ramiss/FPVRaceOne/images/product_files/20260512_200925.jpg

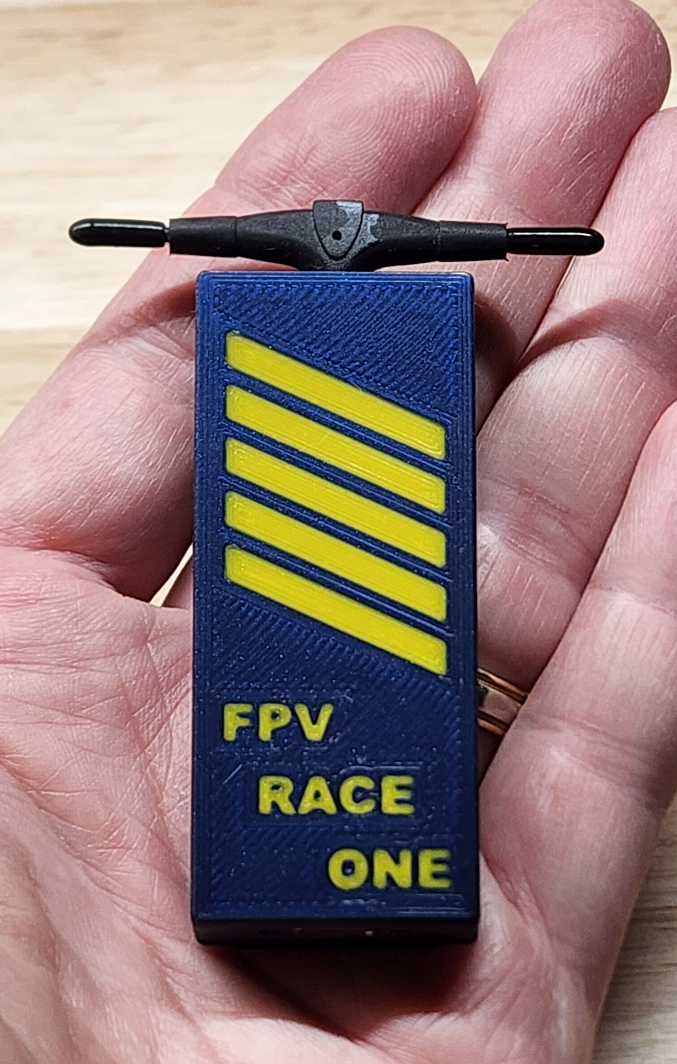
images/product_files/20260512_200925.jpg
