ramiss/FPVRaceOne/images/product_files/FPVRaceOne_Hero.png

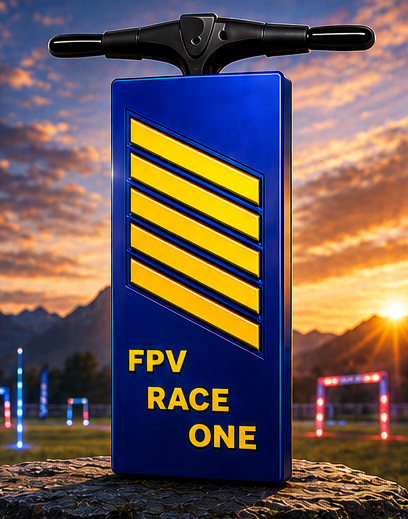
images/product_files/FPVRaceOne_Hero.png
