ramiss/FPVRaceOne/images/product_files/FPVRaceOne_Product.png

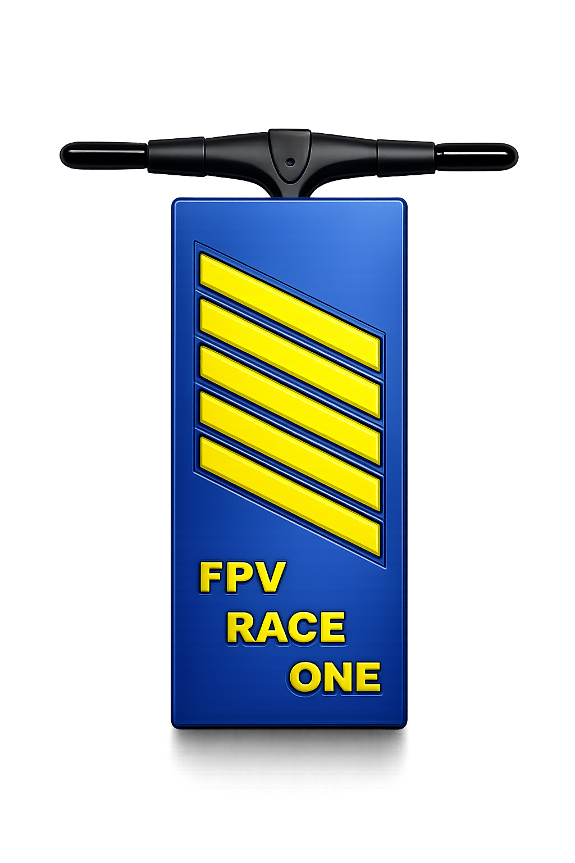
images/product_files/FPVRaceOne_Product.png
