ramiss/FPVRaceOne/images/screenshots/Screenshot 2.png

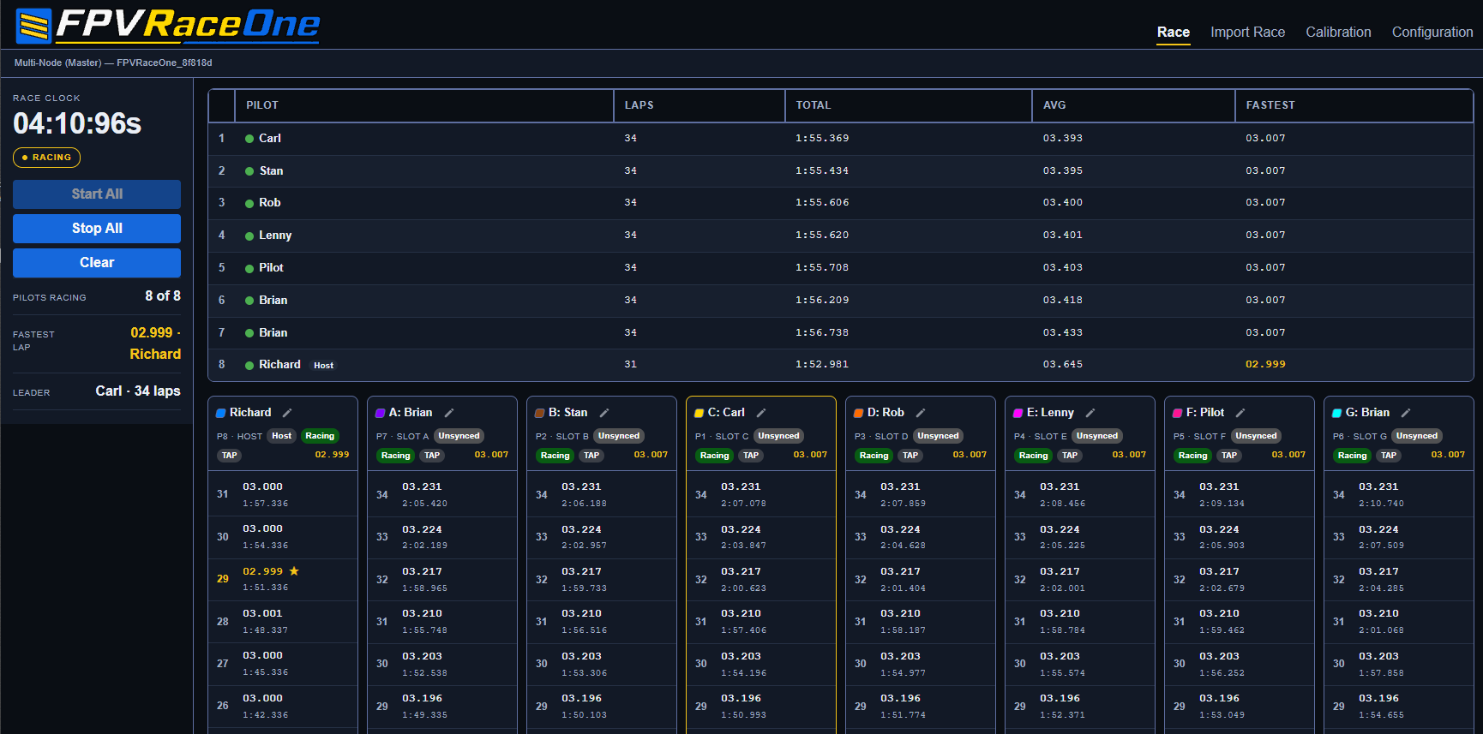
images/screenshots/Screenshot 2.png
