ramiss/FPVRaceOne/images/screenshots/Screenshot Settings 1.png

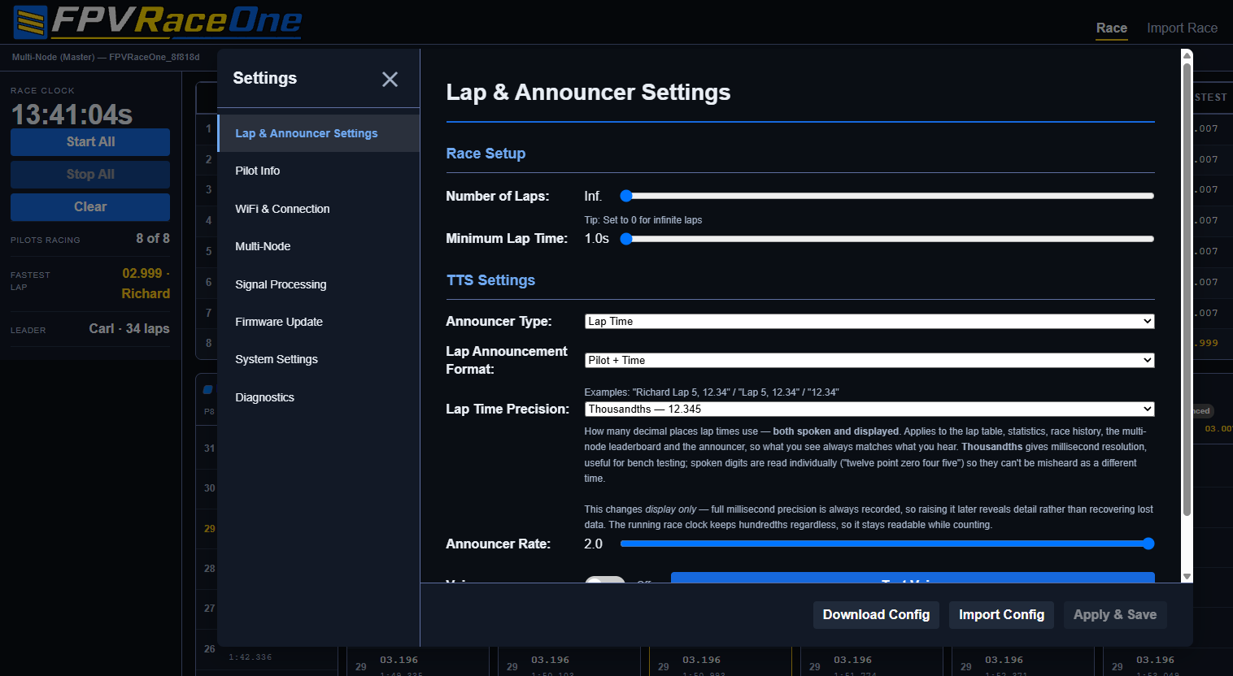
images/screenshots/Screenshot Settings 1.png
