ramiss/FPVRaceOne/images/screenshots/Screenshot Settings 4 Master.png

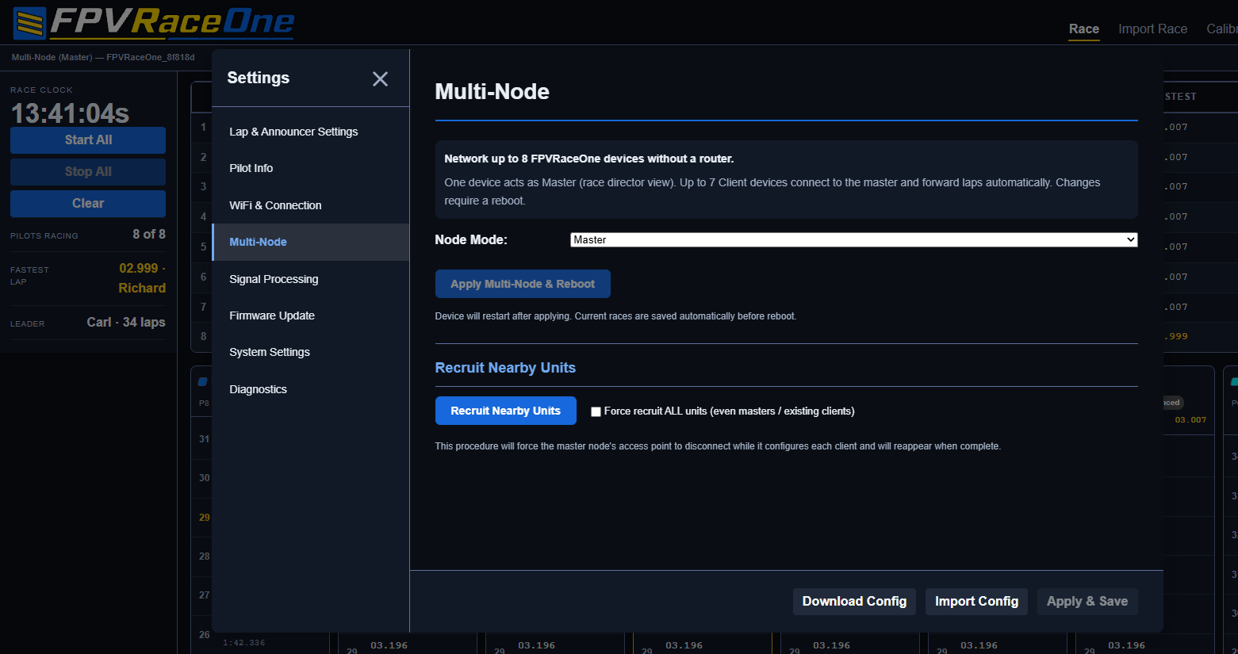
images/screenshots/Screenshot Settings 4 Master.png
