ramiss/FPVRaceOne/images/screenshots/Screenshot Settings 6.png

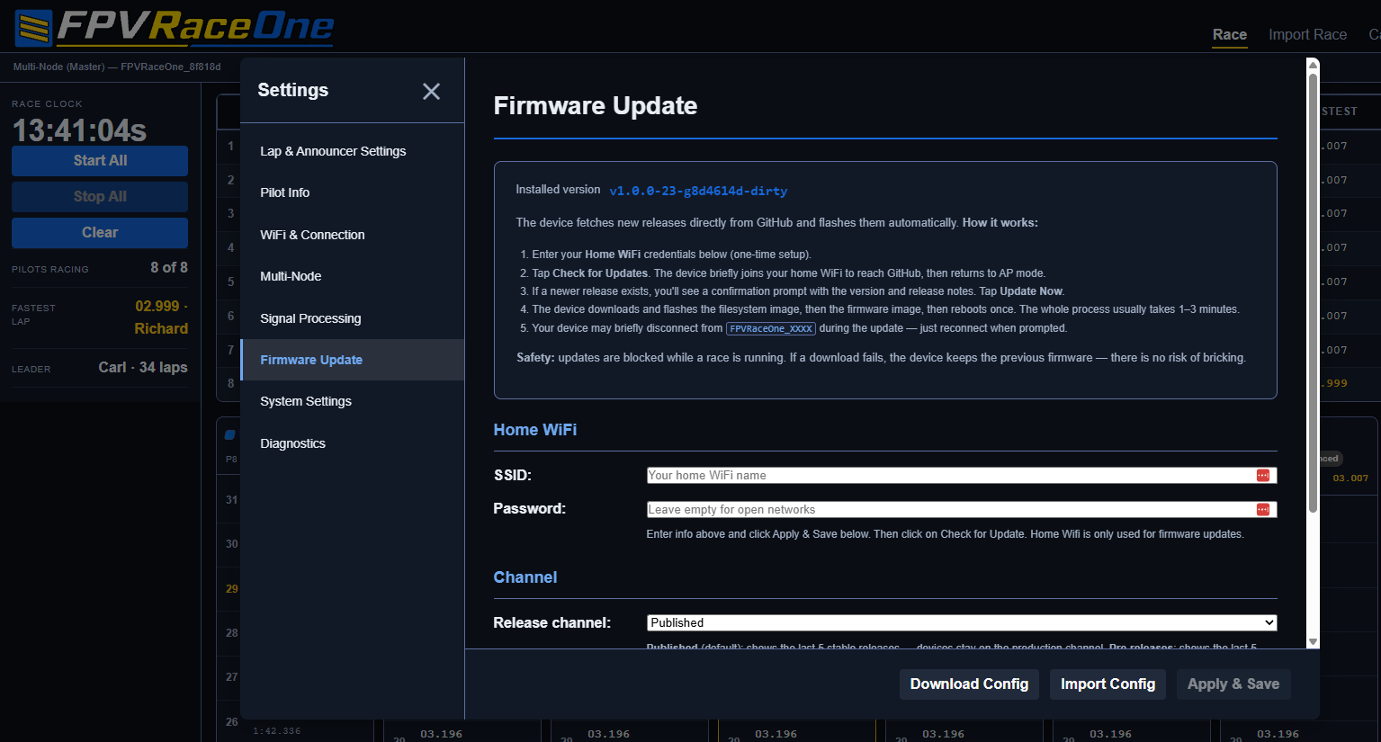
images/screenshots/Screenshot Settings 6.png
