ramiss/FPVRaceOne/images/screenshots/Screenshot Settings 7.png

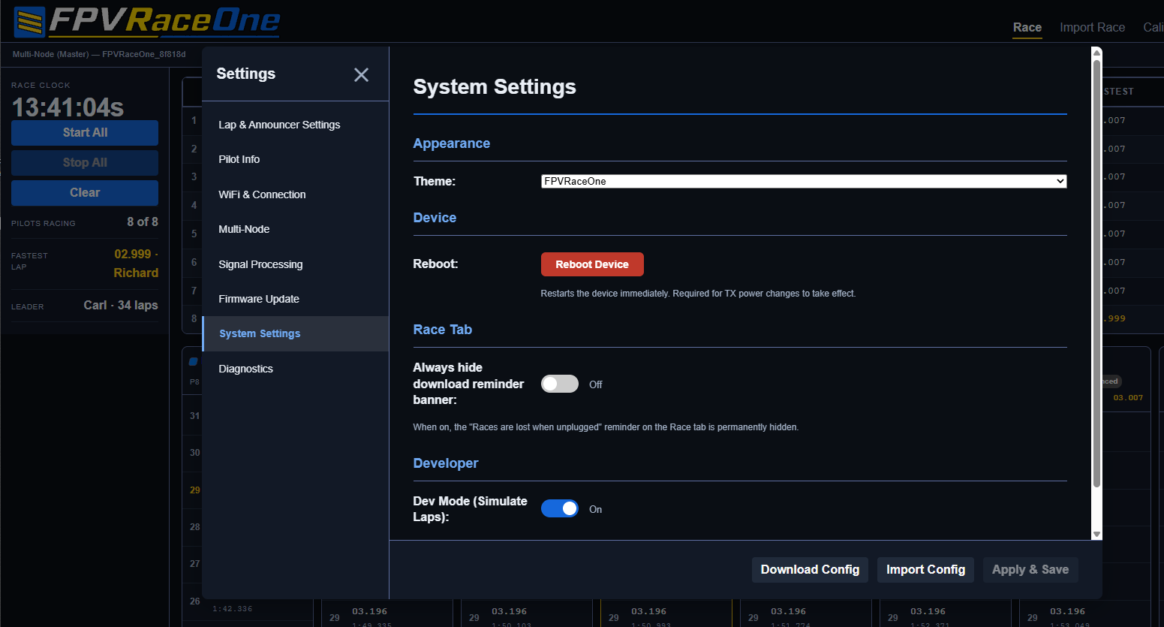
images/screenshots/Screenshot Settings 7.png
