ramiss/FPVRaceOne/images/screenshots/Screenshot Settings 8.png

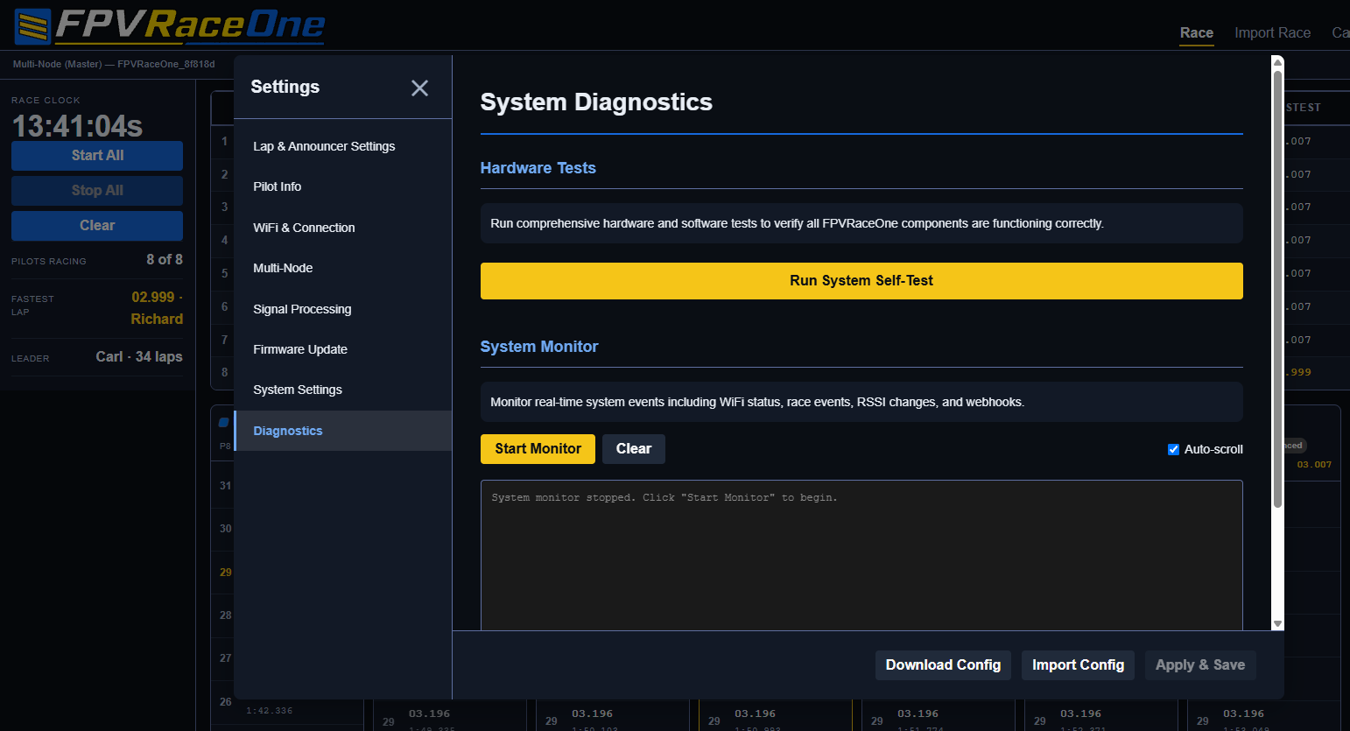
images/screenshots/Screenshot Settings 8.png
