ramiss/FPVRaceOne/images/screenshots/Screenshot Calibration.png

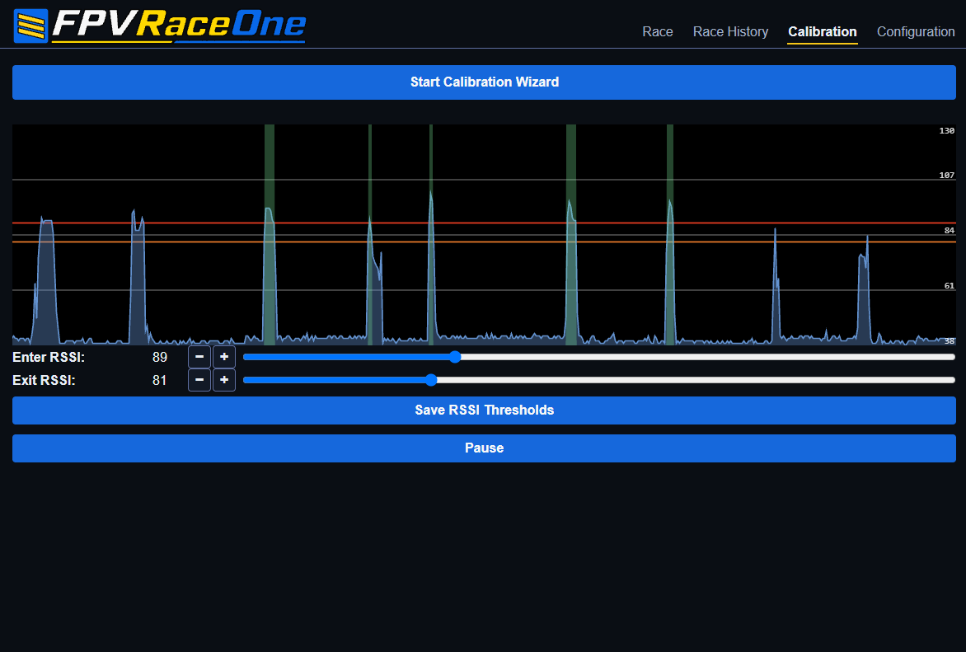
images/screenshots/Screenshot Calibration.png
