ramiss/FPVRaceOne/tools/timing-harness/gui.py

#!/usr/bin/env python3
"""
FPVRaceOne Timing Rig — GUI

Point-and-click front end for harness.py.  Runs the same measurements and adds
plain-language interpretation, because the raw numbers are easy to misread:
bias and jitter mean very different things, and only one of them actually costs
you a lap.

Tkinter deliberately: it ships with Python, so this runs on a clean Windows box
with nothing installed but pyserial (already needed for the harness itself).

    python gui.py

Measurement logic is imported from harness.py rather than duplicated, so the
CLI and GUI can never drift apart.
"""

import json
import os
import queue
import re
import statistics
import sys
import threading
import time
import tkinter as tk
from tkinter import ttk, scrolledtext

try:
    import serial
    from serial.tools import list_ports
except ImportError:
    sys.exit("pyserial not found. Install with:  pip install pyserial")

from harness import (JsonLink, run_once, summarize, open_port_no_reset,
                     measure_transfer, diagnose_transfer, EXPECTED_GAIN,
                     read_device_config, check_interval_vs_minlap, set_min_lap,
                     check_maxlaps_vs_count, emulator_handshake,
                     compute_thresholds, set_thresholds, _fit_line,
                     geometric_detect_ms, plan_envelope,
                     find_min_detectable_width, estimate_search_runs,
                     MultiNodeLoad, probe_master, set_voice_enabled,
                     fetch_director_state, time_director_post, client_targets,
                     fetch_clock_report, analyse_drift_series,
                     race_prearm, race_start, race_stop, fetch_race_clock,
                     DIRECTOR_FANOUT_MS, DIRECTOR_INTERVAL_MS)


# ── Dark theme ──────────────────────────────────────────────────────────────
#
# Picked to sit alongside the product's own dark UI rather than invent a second
# identity: slate panels, a teal accent, and status colours lifted toward the
# lighter end because saturated reds and greens that read well on white go muddy
# on a dark ground.
BG      = "#1a2226"   # window behind everything
PANEL   = "#222c31"   # frames and label frames
FIELD   = "#2a363c"   # entries, buttons, combobox wells
BORDER  = "#35454c"
FG      = "#e2e9ec"
MUTED   = "#93a5ad"
ACCENT  = "#17a589"   # FPVRaceOne teal
ACCENT_HI = "#1bbf9c"
OK_FG   = "#4ade80"
WARN_FG = "#fbbf24"
BAD_FG  = "#f87171"
HEAD_FG = "#ffffff"


def apply_dark_theme(root):
    """Recolour ttk + the classic Tk widgets that ttk styling never reaches."""
    st = ttk.Style()
    # 'clam' rather than 'vista': the native Windows themes draw most of their
    # elements from OS bitmaps and simply ignore background/foreground, so a
    # dark palette applied to them yields dark text on light chrome.
    try:
        st.theme_use("clam")
    except tk.TclError:
        pass

    root.configure(bg=BG)
    st.configure(".", background=PANEL, foreground=FG, fieldbackground=FIELD,
                 bordercolor=BORDER, lightcolor=PANEL, darkcolor=PANEL,
                 troughcolor=BG, focuscolor=ACCENT, insertcolor=FG)
    st.configure("TFrame", background=PANEL)
    st.configure("TLabel", background=PANEL, foreground=FG)
    st.configure("TLabelframe", background=PANEL, bordercolor=BORDER)
    st.configure("TLabelframe.Label", background=PANEL, foreground=ACCENT)
    st.configure("TButton", background=FIELD, foreground=FG,
                 bordercolor=BORDER, padding=(10, 5))
    st.map("TButton",
           background=[("disabled", PANEL), ("pressed", ACCENT),
                       ("active", ACCENT_HI)],
           foreground=[("disabled", MUTED), ("active", "#0f1416")])
    st.configure("TEntry", fieldbackground=FIELD, foreground=FG,
                 bordercolor=BORDER)
    st.configure("TSpinbox", fieldbackground=FIELD, foreground=FG,
                 arrowcolor=FG, bordercolor=BORDER)
    st.configure("TCombobox", fieldbackground=FIELD, background=FIELD,
                 foreground=FG, arrowcolor=FG, bordercolor=BORDER)
    st.map("TCombobox",
           fieldbackground=[("readonly", FIELD)],
           foreground=[("readonly", FG)],
           background=[("readonly", FIELD)])
    st.configure("TCheckbutton", background=PANEL, foreground=FG)
    st.map("TCheckbutton", background=[("active", PANEL)],
           indicatorcolor=[("selected", ACCENT)])
    st.configure("TScale", background=PANEL, troughcolor=FIELD)
    for bar in ("Vertical.TScrollbar", "Horizontal.TScrollbar"):
        st.configure(bar, background=FIELD, troughcolor=BG, arrowcolor=FG,
                     bordercolor=BORDER)
        st.map(bar, background=[("active", ACCENT)])
    # The status bar's sunken relief renders as a light bevel unless told
    # otherwise.
    st.configure("Status.TLabel", background=FIELD, foreground=MUTED,
                 padding=(6, 3))

    # A combobox's dropdown is a classic Tk listbox living in its own toplevel,
    # so no ttk style touches it — it stays glaring white without this.
    root.option_add("*TCombobox*Listbox.background", FIELD)
    root.option_add("*TCombobox*Listbox.foreground", FG)
    root.option_add("*TCombobox*Listbox.selectBackground", ACCENT)
    root.option_add("*TCombobox*Listbox.selectForeground", HEAD_FG)


def style_text_widget(w):
    """Dark-ground a classic Text/ScrolledText, including its caret+selection."""
    w.configure(background=BG, foreground=FG, insertbackground=FG,
                selectbackground=ACCENT, selectforeground=HEAD_FG,
                highlightthickness=0, borderwidth=0)


class FlowFrame(ttk.Frame):
    """A row of widgets that wraps to further rows as the window narrows.

    Tk has no flow layout: pack(side="left") runs children off the edge, and
    grid() shares column widths across rows, which makes ragged-width buttons
    align into gappy columns.  So children are positioned with place() and
    re-laid out on <Configure>, and the frame reports its own height.

    Needed because the button row alone is wider than the window's 760 px
    minimum — on a laptop the last tests were simply unreachable.
    """

    def __init__(self, master, hgap=6, vgap=6, **kw):
        super().__init__(master, **kw)
        self._items = []
        self._hgap = hgap
        self._vgap = vgap
        self._last_w = -1
        self.bind("<Configure>", self._on_configure)

    def add(self, widget, gap_before=0):
        """Append in flow order.  gap_before separates logical groups."""
        self._items.append((widget, gap_before))
        return widget

    def _on_configure(self, ev):
        # Reflow only on a real width change; <Configure> also fires for the
        # height changes we ourselves cause, which would recurse.
        if abs(ev.width - self._last_w) < 2:
            return
        self._last_w = ev.width
        self.reflow(ev.width)

    def reflow(self, width=None):
        if width is None:
            width = self.winfo_width()
        if width <= 1:
            return
        x = y = row_h = 0
        for w, gap_before in self._items:
            ww, wh = w.winfo_reqwidth(), w.winfo_reqheight()
            lead = gap_before if x else 0
            if x and x + lead + ww > width:
                x, y, row_h = 0, y + row_h + self._vgap, 0
                lead = 0
            w.place(x=x + lead, y=y, width=ww, height=wh)
            x += lead + ww + self._hgap
            row_h = max(row_h, wh)
        self.configure(height=y + row_h)


# ── Interpretation ──────────────────────────────────────────────────────────
#
# Thresholds are judgement calls, chosen so a "GOOD" verdict means the effect
# is well below anything that could matter in a race, not merely measurable.

# Mirrored from firmware so measured stalls can be expressed as a duty cycle.
# Keep in step with lib/MULTINODE/multinode.h and multinode.cpp.
FANOUT_THROTTLE_MS       = 2000.0   # MIN_DIRECTOR_BROADCAST_INTERVAL_MS
FANOUT_CLIENT_TIMEOUT_MS = 300      # http.setTimeout() in _broadcastDirectorState
FANOUT_RACE_TIMEOUT_MS   = 500      # http.setTimeout() in _broadcastRaceStart/Stop

JITTER_GOOD_MS = 5.0     # stdev below this is inaudible in a lap time
JITTER_WARN_MS = 15.0
BIAS_NOTE_MS   = 20.0    # bias worth mentioning for cross-device comparison
LAT_GOOD_MS    = 30.0


def _ms(us):
    """Microseconds -> a short millisecond string. '?' when the field is absent.

    Every start-path number on the wire is microseconds; every number a human
    reasons about here is milliseconds.  Converting at the point of display
    keeps the two from being confused in the same sentence.
    """
    if us is None:
        return "?"
    try:
        return "%.0f" % (float(us) / 1000.0)
    except (TypeError, ValueError):
        return "?"


def interpret_interval(res, st, interval_ms, geo_floor_ms=None):
    """Turn interval-test statistics into sentences that say what they mean.

    geo_floor_ms is the earliest a lap could possibly be confirmed for this
    pass width, from envelope geometry alone. Passing it lets the latency
    verdict judge pipeline lag rather than raw latency.
    """
    out = []

    # Before blaming detection, check the RIG actually produced the stimulus.
    # The emulator can reset or lose USB mid-run (a vanishing COM port is the
    # tell), and a stalled rig looks exactly like a device detecting nothing.
    if res.generated >= 0 and res.generated < res.expected:
        out.append(
            f"RIG FAULT — NOT A DEVICE PROBLEM: the emulator reports generating "
            f"only {res.generated} of {res.expected} passes. The device cannot "
            f"detect passes that were never played, so the miss count below is "
            f"the rig's, not the timer's. Check the emulator's USB connection "
            f"(a changing serial-port count is the tell) and re-run."
        )
    elif res.generated < 0:
        out.append(
            f"RIG WARNING: the emulator never sent its 'done' event, so the "
            f"number of passes actually played is unknown. Treat a high miss "
            f"count with suspicion until a clean run confirms the rig."
        )

    missed = res.expected - res.detected
    if missed > 0:
        out.append(
            f"MISSED PASSES: {missed} of {res.expected} generated passes produced "
            f"no lap. That is a detection failure, not a timing one — check the "
            f"enter/exit thresholds and the peak level before reading anything "
            f"below."
        )

    if not st:
        out.append("Not enough laps to compute statistics.")
        return out

    j = st["stdev_ms"]
    if j <= JITTER_GOOD_MS:
        out.append(
            f"CONSISTENCY: GOOD — {j:.2f} ms standard deviation. This is the "
            f"number that actually costs you a lap: lap-time error is the "
            f"difference in jitter between the two crossings, so low jitter "
            f"means repeatable lap times."
        )
    elif j <= JITTER_WARN_MS:
        out.append(
            f"CONSISTENCY: MARGINAL — {j:.2f} ms standard deviation. Visible in "
            f"a lap time but small against typical lap lengths. Worth checking "
            f"whether it grows under multi-node load."
        )
    else:
        out.append(
            f"CONSISTENCY: POOR — {j:.2f} ms standard deviation. Lap times will "
            f"vary noticeably run to run. Check Diagnostics -> RSSI Sample "
            f"Timing for a large worst-gap, which would point at a scheduling "
            f"stall."
        )

    b = st["bias_ms"]
    if abs(b) <= BIAS_NOTE_MS:
        out.append(
            f"BIAS: {b:+.2f} ms. Largely harmless on its own — the same delay "
            f"applies to both crossings of a lap and subtracts out. It matters "
            f"only when comparing two DIFFERENT devices head to head."
        )
    else:
        out.append(
            f"BIAS: {b:+.2f} ms — large. Still mostly cancels within a single "
            f"device's lap times, but two units with different bias would "
            f"disagree by roughly the difference in head-to-head racing."
        )

    if "lat_mean_us" in st:
        lm = st["lat_mean_us"] / 1000.0
        lj = st["lat_stdev_us"] / 1000.0

        # Judge the PIPELINE contribution, not raw latency.  A lap is confirmed
        # on gate exit, so most of the measured figure is simply "the pass had
        # to finish first" — a floor no firmware can beat.  An earlier version
        # compared raw latency against a flat 30 ms and called a perfectly
        # healthy 42 ms "HIGH", which was wrong and alarming.
        floor = geo_floor_ms
        if floor is not None:
            pipe = lm - floor
            if pipe <= 15.0:
                tag = "LATENCY GOOD"
            elif pipe <= 30.0:
                tag = "LATENCY MARGINAL"
            else:
                tag = "LATENCY HIGH"
            out.append(
                f"{tag}: {lm:.2f} ms total, of which {floor:.1f} ms is the pass "
                f"itself and only {pipe:.1f} ms is pipeline lag. A lap is "
                f"confirmed on gate EXIT, not at the peak, so a {res.width_ms} ms "
                f"pass cannot be detected sooner than {floor:.1f} ms no matter "
                f"what the firmware does. The {pipe:.1f} ms is median-filter "
                f"group delay plus the enter debounce."
            )
        else:
            out.append(
                f"LATENCY: {lm:.2f} ms mean, {lj:.2f} ms stdev, stimulus to "
                f"detection. Most of this is the pass width — a lap is confirmed "
                f"on gate exit, not at the peak."
            )

        # Separate real spread from outliers before drawing conclusions.
        if "lat_iqr_us" in st:
            iqr = st["lat_iqr_us"] / 1000.0
            med = st["lat_median_us"] / 1000.0
            outl = st.get("lat_outliers", 0)
            if lj > 2.0 * max(iqr, 0.01) and outl:
                out.append(
                    f"NOTE ON LATENCY SPREAD: stdev is {lj:.2f} ms but the "
                    f"inter-quartile range is only {iqr:.2f} ms, with {outl} "
                    f"outlier(s). The typical pass is tight — the stdev is being "
                    f"inflated by a few stray samples, not by genuine jitter. "
                    f"Median latency is {med:.2f} ms."
                )
            else:
                out.append(
                    f"LATENCY SPREAD: stdev {lj:.2f} ms, IQR {iqr:.2f} ms, "
                    f"median {med:.2f} ms. The two agree, so this is real "
                    f"spread rather than a few outliers."
                )

        if res.dropped:
            out.append(
                f"RIG NOTE: the emulator dropped {res.dropped} marker edge(s) "
                f"because a previous one had not been read yet. Those are lost "
                f"MEASUREMENTS, not missed detections — the device found the "
                f"laps. It only reduces the latency sample count."
            )

        out.append(
            f"IMPORTANTLY, THIS DOES NOT AFFECT LAP TIMES. Lap timing is "
            f"anchored to the recorded PEAK timestamp, not to when detection "
            f"finished, which is why bias is {st['bias_ms']:+.2f} ms despite "
            f"{lm:.0f} ms of detection latency. Latency jitter is {lj:.2f} ms "
            f"yet lap-time jitter is only {st['stdev_ms']:.2f} ms — the "
            f"peak-anchoring is measurably doing its job."
        )
    else:
        out.append(
            "ABSOLUTE LATENCY: not measured — no marker edges seen. Set "
            "TIMING_MARKER_ENABLED to 1 in lib/CONFIG/config.h, reflash, and "
            "confirm D3/GPIO21 is wired to the emulator's GPIO4."
        )

    return out


def interpret_sweep(rows):
    """rows: list of (width_ms, rate, stats-or-None)."""
    out = []
    reliable = [w for w, r, _ in rows if r >= 0.99]
    partial  = [w for w, r, _ in rows if 0.0 < r < 0.99]

    if reliable:
        best = min(reliable)
        out.append(
            f"MINIMUM RELIABLE PASS: {best} ms at >=99% detection. Shorter "
            f"passes than this start to be missed."
        )
        out.append(
            f"For context, a pass whose RSSI envelope is {best} ms wide is a "
            f"very fast gate transit. The narrower this number, the faster the "
            f"drone the pipeline can catch."
        )
    else:
        out.append(
            "NO WIDTH REACHED 99% DETECTION. Either the peak level is too close "
            "to the enter threshold, or calibration does not match the emulated "
            "envelope. Re-run the calibration wizard with the emulator "
            "connected, then retry."
        )

    if partial:
        out.append(
            f"PARTIAL DETECTION between {min(partial)} and {max(partial)} ms — "
            f"this is the roll-off band where the filter starts losing peaks."
        )

    out.append(
        "Compare this figure between polled and DMA modes. If they land in the "
        "same place, DMA peak-hold is not earning its complexity and polled is "
        "the simpler choice."
    )
    return out


# ── Window sizing ───────────────────────────────────────────────────────────

def fit_to_screen(win, want_w, want_h, min_w=760, min_h=520,
                  margin_w=40, margin_h=90):
    """Geometry string for want_w x want_h, shrunk to fit the actual display.

    The rig wants a tall results pane — reading test output is the whole point
    of the tool — but a window taller than the screen pushes the button row and
    the Stop button under the taskbar, where they cannot be clicked.  A short
    pane you can scroll beats a tall one you cannot reach, so the requested
    size is a CEILING, not a promise.

    margin_h covers a title bar plus a taskbar, margin_w a side dock.  Both are
    deliberately generous: losing 90 px of pane is invisible, losing the Stop
    button mid-soak is not.

    Positioned near the top-left rather than centred, so the raw-serial panel
    still has room to dock flush right on a wide display (see _dock_geometry).
    """
    win.update_idletasks()
    sw = win.winfo_screenwidth()
    sh = win.winfo_screenheight()
    w = max(min_w, min(want_w, sw - margin_w))
    h = max(min_h, min(want_h, sh - margin_h))
    x = max(0, min(20, sw - w))
    y = max(0, min(20, sh - h))
    return "%dx%d+%d+%d" % (w, h, x, y)


# ── GUI ─────────────────────────────────────────────────────────────────────

class TimingRigGUI:
    def __init__(self, root):
        self.root = root
        root.title("FPVRaceOne Timing Rig")
        # 1180 is the desktop target; fit_to_screen() clamps it on a laptop so
        # the button row never lands under the taskbar.
        root.geometry(fit_to_screen(root, 880, 1180))
        root.minsize(760, 520)

        self.q = queue.Queue()
        self.worker = None
        self.cancel = threading.Event()

        # Live-monitor state.  Buffers are bounded: this runs for hours between
        # tests and must not grow without limit.
        self._mon_thread = None
        # Ports a running test has claimed; the monitor must not reopen these.
        self._mon_claimed = set()
        self._mon_stop = threading.Event()
        self._mon_resume_after_test = False
        self._mon_lines = {"DUT": [], "EMU": []}
        self._MON_MAX_LINES = 20000
        # Raw serial goes to its own window rather than the results pane, so a
        # long-running monitor cannot bury the test output that gets shared.
        self._log_win = None
        self._log_text = {}
        self._log_follow = {}

        self._build_ports(root)
        self._build_settings(root)
        self._build_buttons(root)
        self._build_output(root)

        # Capture the as-built values BEFORE restoring, so "Reset to Defaults"
        # has something to go back to without re-reading the source.
        self._defaults = {k: v.get() for k, v in self._setting_vars().items()}
        self.restore_settings()

        self.refresh_ports()
        # Listen from launch.  The faults worth catching (the master rebooting
        # itself, the emulator panicking, clients cycling) happen while nobody
        # is running a test, so a monitor that only starts on demand misses
        # exactly the events it exists for.  Deferred slightly so the port
        # comboboxes and the drain loop are live first.
        if self.monitor_on.get():
            self.root.after(300, self._autostart_monitor)
        # Deferred: winfo_* returns 1x1+0+0 until the window manager has mapped
        # the window, so docking computed any earlier lands in the corner.
        if self.log_panel_auto.get():
            self.root.after(120, self._autodock_log_panel)
        self._update_sweep_estimate()   # traces only fire on edit, so seed it
        self.root.after(100, self._drain)

    # -- widgets ------------------------------------------------------------

    def _build_ports(self, root):
        f = ttk.LabelFrame(root, text="Serial ports", padding=8)
        f.pack(fill="x", padx=10, pady=(10, 4))

        ttk.Label(f, text="Emulator (WROOM-32):").grid(row=0, column=0, sticky="w")
        self.emu_cb = ttk.Combobox(f, width=46, state="readonly")
        self.emu_cb.grid(row=0, column=1, padx=6, pady=2)

        ttk.Label(f, text="FPVRaceOne (XIAO C6):").grid(row=1, column=0, sticky="w")
        self.dut_cb = ttk.Combobox(f, width=46, state="readonly")
        self.dut_cb.grid(row=1, column=1, padx=6, pady=2)

        ttk.Button(f, text="Refresh", command=self.refresh_ports)\
            .grid(row=0, column=2, padx=6)
        ttk.Button(f, text="Remember Ports", command=self.remember_ports)\
            .grid(row=1, column=2, padx=6)
        ttk.Button(f, text="Save Settings", command=self.save_settings)\
            .grid(row=0, column=3, padx=6)
        ttk.Button(f, text="Reset to Defaults", command=self.reset_settings)\
            .grid(row=1, column=3, padx=6)

        # Live monitor.  Several faults this session were only visible in raw
        # serial output that no test was capturing at the time — a floating
        # marker pin hanging the emulator, the master self-rebooting on low
        # heap, clients cycling between timeout and re-registration.  Watching
        # continuously, outside a test run, is how those get seen at all.
        self.monitor_on = tk.BooleanVar(value=True)
        # Panel opens docked on launch.  Untick to keep it closed; the choice
        # is saved with the other settings.
        self.log_panel_auto = tk.BooleanVar(value=True)
        ttk.Checkbutton(f, text="Live monitor", variable=self.monitor_on,
                        command=self._toggle_monitor)\
            .grid(row=0, column=4, padx=(12, 2), sticky="w")
        ttk.Button(f, text="Save Logs", command=self.save_logs)\
            .grid(row=1, column=4, padx=(12, 2), sticky="w")
        ttk.Button(f, text="Log Panel \u2197", command=self.open_log_panel)\
            .grid(row=0, column=5, padx=(6, 2))
        ttk.Checkbutton(f, text="auto-dock", variable=self.log_panel_auto)\
            .grid(row=1, column=5, padx=(6, 2), sticky="w")

    def _build_settings(self, root):
        # Settings are grouped by WHICH TEST USES THEM.  A single flat panel
        # put "Width" and "Sweep widths" side by side with no indication that
        # each is read by a different button and ignored by the other, which
        # is a fair way to confuse someone.
        self.vars = {}

        # ── Shared: the envelope every test drives the emulator with ────────
        f = ttk.LabelFrame(root, text="Signal — used by all tests", padding=8)
        f.pack(fill="x", padx=10, pady=(4, 2))

        def spin(parent, col, label, key, default, lo, hi, tip="", row=0):
            ttk.Label(parent, text=label).grid(row=row, column=col * 2,
                                               sticky="e", padx=(8, 2))
            v = tk.StringVar(value=str(default))
            ttk.Spinbox(parent, from_=lo, to=hi, textvariable=v, width=8)\
                .grid(row=row, column=col * 2 + 1, sticky="w")
            self.vars[key] = v
            if tip:
                ttk.Label(parent, text=tip, foreground="#666", font=("", 8))\
                    .grid(row=row + 1, column=col * 2, columnspan=2,
                          sticky="w", padx=(8, 2))

        spin(f, 0, "Baseline:", "baseline", 40, 0, 255, "at rest")
        spin(f, 1, "Peak:", "peak", 200, 0, 255, "at apex")
        spin(f, 2, "Interval (ms):", "interval", 3000, 100, 60000, "pass to pass")
        spin(f, 3, "Count:", "count", 30, 2, 500, "passes per run")

        # Min Lap discards any crossing sooner than its threshold (default
        # 5000 ms).  Zeroing it lets the rig use short intervals, which turns a
        # 16-minute sweep into about 4.  Restored afterwards.
        self.zero_minlap = tk.BooleanVar(value=False)
        ttk.Checkbutton(f, text="Force device Min Lap = 0 during run (restored after)",
                        variable=self.zero_minlap)\
            .grid(row=2, column=0, columnspan=8, sticky="w", padx=(8, 0), pady=(6, 0))

        # Announcements are rendered in the browser, never on the device, so
        # muting them cannot affect the measurement — it just spares a long
        # TTS backlog after a 30-lap run.
        self.mute_voice = tk.BooleanVar(value=False)
        ttk.Checkbutton(f, text="Mute device announcements during run "
                                "(restored after; refresh the browser tab to apply)",
                        variable=self.mute_voice)\
            .grid(row=3, column=0, columnspan=8, sticky="w", padx=(8, 0), pady=(2, 0))

        # ── Test 3 only ────────────────────────────────────────────────────
        f3 = ttk.LabelFrame(root, text="Test 3 only — Accuracy + Consistency",
                            padding=8)
        f3.pack(fill="x", padx=10, pady=2)
        spin(f3, 0, "Pass width (ms):", "width", 40, 1, 1000,
             "one fixed width; measures jitter at that width")

        # ── Test 4 only ────────────────────────────────────────────────────
        # Binary search rather than a hand-written list of widths: a list
        # spends most of its runs far from the boundary while still only
        # resolving to whatever spacing was typed.  The search halves until
        # detection fails, then bisects — same answer, fewer runs, and to a
        # stated precision.
        f4 = ttk.LabelFrame(root, text="Test 4 only — Min Pass Width "
                                       "(automatic search)", padding=8)
        f4.pack(fill="x", padx=10, pady=2)

        spin(f4, 0, "Start width (ms):", "sweep_start", 100, 5, 1000,
             "must detect reliably")
        spin(f4, 1, "Resolution (ms):", "sweep_res", 2, 1, 50,
             "how precisely to find it")
        spin(f4, 2, "Passes per step:", "sweep_count", 10, 3, 100,
             "more = slower, surer")
        spin(f4, 3, "Require (%):", "sweep_require", 90, 50, 100,
             "counts as 'detects'")

        # ── Multi-node load (optional, applies to tests 3 and 4) ───────────
        # Drives the master's expensive path — inbound lap -> blocking
        # directorState fanout to every registered client — at a known rate,
        # while the timing test runs underneath.  Real clients must be
        # registered: handleLap rejects unknown nodeIds and the fanout needs
        # somewhere to go.
        fL = ttk.LabelFrame(root, text="Multi-node load (optional) — applies to "
                                       "tests 3 and 4", padding=8)
        fL.pack(fill="x", padx=10, pady=2)

        self.load_on = tk.BooleanVar(value=False)
        ttk.Checkbutton(fL, text="Generate master load during the run",
                        variable=self.load_on)\
            .grid(row=0, column=0, columnspan=6, sticky="w", padx=(8, 0))

        # A master serves its AP on 192.168.5.1 (MULTINODE_MASTER_IP); a
        # single/standalone unit uses 192.168.4.1.  Default to the master
        # address, since load testing only applies in multi-node mode.
        ttk.Label(fL, text="Master IP:").grid(row=1, column=0, sticky="e", padx=(8, 2))
        self.master_ip = tk.StringVar(value="192.168.5.1")
        ttk.Entry(fL, textvariable=self.master_ip, width=16)\
            .grid(row=1, column=1, sticky="w")

        ttk.Label(fL, text="Node IDs:").grid(row=1, column=2, sticky="e", padx=(8, 2))
        self.load_nodes = tk.StringVar(value="1,2")
        ttk.Entry(fL, textvariable=self.load_nodes, width=12)\
            .grid(row=1, column=3, sticky="w")

        ttk.Label(fL, text="Pattern:").grid(row=1, column=4, sticky="e", padx=(8, 2))
        self.load_mode = tk.StringVar(value="burst")
        ttk.Combobox(fL, textvariable=self.load_mode, width=7, state="readonly",
                     values=("burst", "spread")).grid(row=1, column=5, sticky="w")

        ttk.Label(fL, text="Lap (s):").grid(row=1, column=6, sticky="e", padx=(8, 2))
        self.burst_interval = tk.StringVar(value="3.0")
        ttk.Entry(fL, textvariable=self.burst_interval, width=6)\
            .grid(row=1, column=7, sticky="w")

        ttk.Label(fL, text="Quiet before stop (s):").grid(row=2, column=4, sticky="e", padx=(8, 2))
        self.stop_delay = tk.StringVar(value="0")
        ttk.Entry(fL, textvariable=self.stop_delay, width=6)            .grid(row=2, column=5, sticky="w")
        ttk.Label(fL, text="Pack (ms):").grid(row=1, column=8, sticky="e", padx=(8, 2))
        self.burst_spread = tk.StringVar(value="10")
        ttk.Entry(fL, textvariable=self.burst_spread, width=6)\
            .grid(row=1, column=9, sticky="w")

        # Kept for 'spread' mode and for comparison against earlier results.
        self.load_rate = tk.StringVar(value="2.0")

        ttk.Label(fL, text="Source IPs:").grid(row=2, column=0, sticky="e", padx=(8, 2))
        self.load_srcs = tk.StringVar(value="")
        ttk.Entry(fL, textvariable=self.load_srcs, width=30)\
            .grid(row=2, column=1, columnspan=3, sticky="w", pady=(2, 0))
        ttk.Label(fL, text="blank = let the OS choose. Two comma-separated local "
                           "IPs splits the load across both WiFi adapters as "
                           "independent stations.",
                  foreground="#666", font=("", 8))\
            .grid(row=3, column=0, columnspan=6, sticky="w", padx=(8, 2))

        ttk.Button(fL, text="Check master", command=self.check_master)\
            .grid(row=1, column=6, padx=(10, 0))

        self.sweep_est = ttk.Label(f4, text="", foreground="#666", font=("", 8))
        self.sweep_est.grid(row=2, column=0, columnspan=8, sticky="w",
                            padx=(8, 2), pady=(6, 0))
        for k in ("sweep_start", "sweep_res", "sweep_count", "interval"):
            self.vars[k].trace_add("write", lambda *_: self._update_sweep_estimate())

        # Was needed when the polled and DMA paths had ~1.9x different ADC
        # gain: identical DAC values gave each mode a different RSSI envelope.
        # The firmware now scales the DMA path to match, so raw DAC values are
        # directly comparable again and this is OFF by default — leaving it on
        # would actually MASK a residual gain mismatch by silently correcting
        # for it, which is the opposite of what you want while verifying.
        #
        # Turn it on when the envelope must be pinned regardless of gain, e.g.
        # on a chip whose RSSI_DMA_GAIN_NUM has not been re-derived.
        self.target_rssi = tk.BooleanVar(value=False)
        ttk.Checkbutton(f, text="Baseline/Peak are RSSI targets (off = raw DAC; "
                                "on = pin the envelope regardless of gain)",
                        variable=self.target_rssi)\
            .grid(row=4, column=0, columnspan=8, sticky="w", padx=(8, 0), pady=(2, 0))

    def run_drift(self):
        # Needs NOTHING but the network.  Clock probing runs continuously in
        # steady state, so this neither starts a race nor touches a serial
        # port — both monitors stay live for the whole run.
        self._start(self._drift_worker, needs=())

    # ── Race sync ───────────────────────────────────────────────────────────
    #
    # Everything about the start path -- pre-arm, the clock-sync burst, the
    # scheduled fleet instant, the GO datagram, the ack, the repair pass -- was
    # built and debugged with no automated coverage, because the rig started
    # races over SERIAL and serial calls the timer directly.  Every regression
    # in that work was therefore caught by a human watching two screens.
    #
    # This drives the same three endpoints the director's browser drives, so
    # the real path runs, and then asserts the four things that path promises.
    RACE_SYNC_TOL_MS = 50.0        # cross-fleet start spread we accept
    RACE_SYNC_SETTLE_S = 12.0      # pre-arm window before GO; a countdown is ~18 s

    def run_race_sync(self):
        # Network only.  No serial, so both monitors stay live and the fleet
        # under test is the real one, not an emulator.
        self._start(self._race_sync_worker, needs=())

    def _race_sync_worker(self):
        try:
            master = self.master_ip.get().strip()
            try:
                rounds = max(1, int(self.sync_rounds.get()))
            except (TypeError, ValueError):
                rounds = 3

            self.emit("\n" + "=" * 66 + "\n", "dim")
            self.emit("RACE SYNC\n", "head")
            self.emit("Drives prearm -> GO -> stop over HTTP, %d time(s), and checks:\n"
                      "  1. every client acknowledged the GO datagram\n"
                      "  2. the fleet's race clocks agree within %.0f ms\n"
                      "  3. the start margin does NOT ratchet race over race\n"
                      "  4. a start with no pre-arm mints a FRESH race epoch\n"
                      "No quad required -- this measures the start path, not laps.\n\n"
                      % (rounds, self.RACE_SYNC_TOL_MS), "dim")

            nodes = probe_master(master)
            if not isinstance(nodes, dict):
                self.emit("  Master at %s did not answer. Needs master mode.\n"
                          % master, "bad")
                return
            targets = client_targets(nodes)
            if not targets:
                self.emit("  No online clients. This test needs at least one.\n", "bad")
                return
            self.emit("  %d client(s): %s\n\n"
                      % (len(targets),
                         ", ".join("%s(%s)" % (t[2], t[0]) for t in targets)), "dim")

            # Clean slate: a race left running from a previous session would
            # make round 1 measure a stop, not a start.
            race_stop(master)
            self.cancel.wait(1.5)

            boosts = []
            worst_spread = 0.0
            failures = []
            seen_race_ids = []

            for r in range(1, rounds + 1):
                if self.cancel.is_set():
                    break
                self.emit("  -- round %d --\n" % r, "head")
                st, _ = race_prearm(master)
                if st != 200:
                    failures.append("round %d: prearm returned %s" % (r, st))
                    self.emit("    prearm FAILED (%s)\n" % st, "bad")
                    break

                # Let the sync burst run.  Cutting this short does not just make
                # the test unrealistic -- it starves the very measurement the
                # start instant is computed from.
                self._await_sync(master, self.RACE_SYNC_SETTLE_S)

                st, _ = race_start(master)
                if st != 200:
                    failures.append("round %d: start returned %s" % (r, st))
                    self.emit("    start FAILED (%s)\n" % st, "bad")
                    break

                # Past the start margin (max 2.5 s) plus the verify grace, so
                # acks have landed and any repair has already happened.
                self.cancel.wait(4.0)

                spread, det = self._measure_start_spread(master, targets)
                rep = fetch_clock_report(master) or {}
                boost = rep.get("startBoostUs")
                if boost is not None:
                    boosts.append(boost)

                unacked = [n.get("nodeId") for n in rep.get("nodes", []) or []
                           if n.get("online") and n.get("clockValid")
                           and not n.get("startAcked")]
                late = [(n.get("nodeId"), n.get("startLateMs"))
                        for n in rep.get("nodes", []) or []
                        if (n.get("startLateMs") or 0) > 0]

                for line, tag in det:
                    self.emit(line, tag)
                if spread is not None:
                    worst_spread = max(worst_spread, spread)
                    self.emit("    start spread %.1f ms  (margin %s ms, boost %s ms)\n"
                              % (spread,
                                 _ms(rep.get("startMarginUs")), _ms(boost)),
                              "ok" if spread <= self.RACE_SYNC_TOL_MS else "bad")
                    if spread > self.RACE_SYNC_TOL_MS:
                        failures.append("round %d: start spread %.1f ms" % (r, spread))
                else:
                    failures.append("round %d: could not measure spread" % r)
                    self.emit("    could not read every node's clock\n", "bad")

                if unacked:
                    failures.append("round %d: no GO ack from node(s) %s"
                                    % (r, unacked))
                    self.emit("    NO GO ACK from node(s) %s -- these fell back to\n"
                              "    the HTTP repair path\n"
                              % ", ".join(str(x) for x in unacked), "bad")
                if late:
                    self.emit("    started late: %s\n"
                              % ", ".join("node %s +%s ms" % (a, b) for a, b in late),
                              "warn")

                ds = fetch_director_state(master)[1] or {}
                rid = (ds.get("race") or {}).get("raceId")
                seen_race_ids.append(rid)

                race_stop(master)
                self.cancel.wait(1.0)

                # After a stop the fleet must HOLD its final time, not zero it.
                ds = fetch_director_state(master)[1] or {}
                final = (ds.get("race") or {}).get("elapsedMs")
                if not final:
                    failures.append("round %d: master zeroed its clock on stop" % r)
                    self.emit("    master's clock reset to 0 on stop (should hold "
                              "the final time)\n", "bad")
                else:
                    self.emit("    final time held at %.2f s\n" % (final / 1000.0), "ok")
                self.cancel.wait(2.0)

            self._race_sync_epoch_check(master, seen_race_ids, failures)
            self._race_sync_verdict(boosts, worst_spread, failures)
        except Exception as e:
            self.emit("  Race sync failed: %s\n" % e, "bad")
        finally:
            try:
                race_stop(self.master_ip.get().strip())
            except Exception:
                pass

    def _await_sync(self, master, seconds):
        """Hold open the pre-arm window and report what the burst achieved."""
        deadline = time.time() + seconds
        best = {}
        while time.time() < deadline and not self.cancel.is_set():
            rep = fetch_clock_report(master)
            for n in (rep or {}).get("nodes", []) or []:
                if n.get("online") and n.get("clockValid"):
                    d = n.get("delayUs")
                    if d and d > 0:
                        nid = n.get("nodeId")
                        best[nid] = min(best.get(nid, d), d)
            self.cancel.wait(1.0)
        if best:
            self.emit("    synced %d node(s), best delay %.1f-%.1f ms\n"
                      % (len(best), min(best.values()) / 1000.0,
                         max(best.values()) / 1000.0), "dim")
        else:
            self.emit("    NO node reported a valid clock offset after %.0f s\n"
                      "    -- every start below will use the degraded HTTP path\n"
                      % seconds, "warn")

    def _measure_start_spread(self, master, targets):
        """Largest disagreement between any two race clocks, in ms.

        Each device is asked for its own elapsed, and each answer is corrected
        back to a common PC-clock instant.  A device that started early reads
        HIGH once corrected, so the spread across the fleet IS the start spread
        -- no device has to know about any other for this to work.
        """
        ref = time.time() + 0.001
        readings = []
        detail = []
        for ip, label in [(master, "master")] + [(t[1], "node %s" % t[0]) for t in targets]:
            ms, running, t_mid = fetch_race_clock(ip)
            if ms is None or not running:
                detail.append(("    %s: not running (%s)\n" % (label, ms), "bad"))
                continue
            corrected = ms - (t_mid - ref) * 1000.0
            readings.append((label, corrected))
        if len(readings) < 2:
            return None, detail
        lo = min(v for _, v in readings)
        for label, v in readings:
            detail.append(("    %-9s %8.0f ms  (%+6.1f ms)\n" % (label, v, v - lo), "dim"))
        return max(v for _, v in readings) - lo, detail

    def _race_sync_epoch_check(self, master, seen_race_ids, failures):
        """A start with NO pre-arm must mint a fresh epoch, not reuse the last.

        Reusing it is exactly the "run 2 inherits run 1's laps" failure the
        epoch system exists to prevent, and it is reachable in the field: a
        pre-arm POST that fails while the browser countdown proceeds anyway.
        """
        self.emit("\n  -- epoch check (start with no pre-arm) --\n", "head")
        # `or {}` on the inner get as well: a present-but-null "race" key would
        # make .get("race", {}) hand back None and crash mid-run, leaving a race
        # running on the fleet.  Same pattern as the round loop above.
        before = ((fetch_director_state(master)[1] or {}).get("race") or {}).get("raceId")
        st, _ = race_start(master)
        if st != 200:
            self.emit("    start returned %s -- skipped\n" % st, "warn")
            return
        self.cancel.wait(3.5)
        after = ((fetch_director_state(master)[1] or {}).get("race") or {}).get("raceId")
        race_stop(master)
        if before and after and before == after:
            failures.append("start without pre-arm reused epoch %s" % before)
            self.emit("    REUSED epoch %s -- a second race would inherit the\n"
                      "    first's laps\n" % before, "bad")
        else:
            self.emit("    epoch %s -> %s (fresh)\n" % (before, after), "ok")

    def _race_sync_verdict(self, boosts, worst_spread, failures):
        self.emit("\n  What this means\n", "head")
        if boosts:
            self.emit("    start boost across rounds: %s\n"
                      % " -> ".join(_ms(b) + " ms" for b in boosts), "dim")
            # The ratchet is the failure that hides: each race that "repairs" a
            # node adds 150 ms and only a perfectly clean race gives 25 ms back.
            # A pilot with "ignore race director" set made a clean race
            # impossible, so the margin climbed to its 1 s cap and stayed there.
            if len(boosts) >= 2 and boosts[-1] > boosts[0]:
                failures.append("start margin ratcheted: %s -> %s us"
                                % (boosts[0], boosts[-1]))
                self.emit("    RATCHETING: the boost grew across rounds, so some\n"
                          "    node is being counted as a missed start every race.\n"
                          "    Check for a client with 'ignore race director' set.\n",
                          "bad")
            else:
                self.emit("    boost is flat or decaying -- no phantom repairs.\n", "ok")

        if failures:
            self.emit("\n  FAILED (%d):\n" % len(failures), "bad")
            for f in failures:
                self.emit("    - %s\n" % f, "bad")
        else:
            self.emit("\n  PASS: every client acked GO, clocks agreed within\n"
                      "  %.1f ms (worst %.1f ms), the margin did not ratchet, and\n"
                      "  each race got its own epoch.\n"
                      % (self.RACE_SYNC_TOL_MS, worst_spread), "ok")

    def _drift_worker(self):
        """Log every node's raw clock offset, then fit drift over the whole run.

        WHY this exists: the firmware fits drift over a rolling 8-sample window
        (~1000 s span), which at the probe noise we measure gives a standard
        error near 6 ppm -- so its readings of -8/-5/+1/-4 ppm are all within
        1 sigma of zero and cannot be distinguished from no drift at all.
        A longer baseline shrinks that error as 1/span, so an hour of samples
        settles in minutes of analysis what the device cannot settle at all.

        Fits rawOffsetUs, never offsetUs: the latter is min-delay filtered and
        only steps when a better sample lands, so fitting it measures the
        filter rather than the crystals.

        The question is NOT "what is the drift" to high precision.  It is:
          1. is each node's value REPEATABLE (a per-unit crystal signature),
             or does it wander through the same range (noise)?
          2. does any node exceed ~10 ppm, the point where correcting it moves
             a lap by more than the offset error already does?
        """
        try:
            master = self.master_ip.get().strip()
            try:
                mins = max(1.0, float(self.drift_mins.get()))
            except (TypeError, ValueError):
                mins = 60.0
            period_s = 30.0

            self.emit("\n" + "=" * 66 + "\n", "dim")
            self.emit("CLOCK DRIFT LOG\n", "head")
            self.emit("Polls /api/multinode/clocks every %.0f s for %.0f min and fits\n"
                      "each node's raw offset over the whole run.\n"
                      "No race required -- drift probing runs continuously.\n\n"
                      % (period_s, mins), "dim")
            if mins < 30:
                self.emit("  NOTE: under 30 min the fit's error bar will still be\n"
                          "  several ppm, which is the size of the effect. 60+ min\n"
                          "  is what actually settles the question.\n\n", "warn")

            first = fetch_clock_report(master)
            if not isinstance(first, dict):
                self.emit("  Master at %s did not answer /api/multinode/clocks.\n"
                          "  Needs master mode and firmware with the clock report.\n"
                          % master, "bad")
                return

            # Same logs/ directory save_logs() uses, so a drift run lands
            # alongside the serial captures from the same session.
            out_dir = os.path.join(os.path.dirname(os.path.abspath(__file__)), "logs")
            os.makedirs(out_dir, exist_ok=True)
            stamp = time.strftime("%Y%m%d-%H%M%S")
            csv_path = os.path.join(out_dir, "%s-clockdrift.csv" % stamp)
            # (rawAtUs, rawOffsetUs, rawDelayUs, bootId) -- DEDUPED.  delay and
            # bootId travel WITH each sample rather than in a parallel list:
            # the analysis filters and segments on them, so they have to stay
            # aligned to the point they describe.
            series = {}      # nodeId -> [(at, off, delay, bootId)]
            ppm_hist = {}    # nodeId -> [firmware driftPpm readings]
            clamped = set()  # nodeIds whose firmware fit hit the +/-100 ppm rail
            reboots = {}     # nodeId -> count of bootId changes seen
            last_boot = {}   # nodeId -> last bootId seen
            last_at = {}     # nodeId -> rawAtUs of the sample already recorded
            dupes = 0

            deadline = time.time() + mins * 60.0
            polls = 0
            with open(csv_path, "w", encoding="utf-8", newline="") as fh:
                fh.write("wallClock,masterUs,rawAtUs,nodeId,rawOffsetUs,rawDelayUs,"
                         "offsetUs,delayUs,driftPpm,driftValid,driftClamped,"
                         "driftSamples,samples,bootId\n")
                while time.time() < deadline and not self.cancel.is_set():
                    rep = fetch_clock_report(master)
                    if isinstance(rep, dict):
                        polls += 1
                        m_us = rep.get("masterUs")
                        wall = time.strftime("%H:%M:%S")
                        for n in rep.get("nodes", []) or []:
                            if not isinstance(n, dict) or not n.get("online"):
                                continue
                            nid = n.get("nodeId")
                            raw = n.get("rawOffsetUs")
                            at  = n.get("rawAtUs")
                            if nid is None or raw is None:
                                continue
                            boot = n.get("bootId")
                            fh.write("%s,%s,%s,%s,%s,%s,%s,%s,%s,%s,%s,%s,%s,%s\n" % (
                                wall, m_us, at, nid, raw, n.get("rawDelayUs"),
                                n.get("offsetUs"), n.get("delayUs"),
                                n.get("driftPpm"), n.get("driftValid"),
                                n.get("driftClamped"),
                                n.get("driftSamples"), n.get("samples"), boot))
                            if n.get("driftValid"):
                                ppm_hist.setdefault(nid, []).append(n.get("driftPpm"))
                            # A clamped fit is the firmware saying "this reading
                            # ran away", not "this node drifts at 100 ppm".
                            if n.get("driftClamped"):
                                clamped.add(nid)
                            # Reboots are reported live: two clients restarting
                            # during an idle hour is its own defect, and burying
                            # it in the summary is how it went unnoticed before.
                            if boot and last_boot.get(nid) not in (None, boot):
                                reboots.setdefault(nid, []).append(
                                    n.get("resetReason") or "UNKNOWN")
                                self.emit("    node %s REBOOTED: %s  (bootId %s -> %s)\n"
                                          % (nid, n.get("resetReason") or "?",
                                             last_boot[nid], boot), "warn")
                            if boot:
                                last_boot[nid] = boot

                            # DEDUPE, and use the probe's OWN timestamp.
                            #
                            # Probing is round-robin at one node per 25 s, so on
                            # a six-client fleet each node yields a fresh sample
                            # only every ~150 s -- far slower than we poll.
                            # Counting the same sample five times would inflate
                            # n without adding information and shrink the error
                            # bar by ~sqrt(5), producing a confident number
                            # built on correlated points.  That is the exact
                            # mistake this tool exists to detect.
                            if at is None or last_at.get(nid) == at:
                                if at is not None:
                                    dupes += 1
                                continue
                            last_at[nid] = at
                            series.setdefault(nid, []).append(
                                (at, raw, n.get("rawDelayUs"), boot))
                        fh.flush()
                        if polls % 10 == 0:
                            left = max(0, deadline - time.time())
                            self.emit("    %d polls, %.0f min left\n" % (polls, left / 60.0),
                                      "dim")
                    # Interruptible sleep: Stop takes effect within the poll,
                    # not at the end of a 30 s nap.
                    self.cancel.wait(period_s)

            got = sum(len(v) for v in series.values())
            self.emit("\n  Wrote %s\n" % csv_path, "head")
            self.emit("  %d polls -> %d independent samples (%d repeat reads "
                      "discarded)\n" % (polls, got, dupes), "dim")
            self._report_drift(series, ppm_hist, clamped, reboots)
        except Exception as e:
            self.emit("  Drift log failed: %s\n" % e, "bad")

    def _report_drift(self, series, ppm_hist, clamped, reboots):
        """Independent fit + the repeatability test, side by side.

        Only nodes whose series is CLEAN reach `fits`.  A node that restarted
        mid-run is excluded outright rather than fitted: its esp_timer drops by
        its whole prior uptime, and a line through that step reports the uptime
        as a rate.  That is not a conservative reading, it is a wrong one, and
        it previously dominated the worst-case figure by five orders of
        magnitude.
        """
        self.emit("\n  What this means\n", "head")
        if not series:
            self.emit("  - No samples collected. Are clients online?\n", "bad")
            return

        MATERIAL_PPM = 10.0     # below this, correcting moves a lap < 3 ms / 5 min
        fits = {}
        excluded = []
        for nid in sorted(series):
            pts = series[nid]
            res = analyse_drift_series(pts)
            fw = ppm_hist.get(nid) or []
            fw_txt = ""
            if fw:
                fw_txt = "   firmware %+.0f..%+.0f ppm" % (min(fw), max(fw))
                if nid in clamped:
                    fw_txt += " (CLAMPED - not a measurement)"

            delays = [p[2] for p in pts if p[2]]
            med_delay = statistics.median(delays) if delays else 0

            if res["status"] == "discontinuity":
                excluded.append(nid)
                why = res["breaks"][0] if res["breaks"] else "series is not continuous"
                self.emit("    node %-2s  EXCLUDED - %s\n" % (nid, why), "bad")
                self.emit("              a fit across this would report the node's\n"
                          "              uptime as a drift rate, not its crystal.\n", "dim")
                continue
            if res["status"] == "implausible":
                excluded.append(nid)
                self.emit("    node %-2s  EXCLUDED - fit came out %+.0f ppm, beyond\n"
                          "              anything quartz does. Bad probes or an\n"
                          "              undetected restart.\n" % (nid, res["ppm"]), "bad")
                continue
            if res["status"] != "ok":
                self.emit("    node %-2s  not enough spread yet "
                          "(%d samples, %.0f min)\n"
                          % (nid, res["total_samples"], res["span_s"] / 60.0), "warn")
                continue

            ppm, se, n = res["ppm"], res["stderr"], res["n"]
            fits[nid] = (ppm, se)
            note = ""
            if res["segments"] > 1:
                note = "  [longest of %d segments]" % res["segments"]
            self.emit("    node %-2s  %+7.2f +/- %.2f ppm  (n=%d, delay med %.1f ms)%s%s\n"
                      % (nid, ppm, se, n, med_delay / 1000.0, fw_txt, note), "ok")

        if reboots:
            self.emit("\n  - %d node(s) RESTARTED during this run:\n" % len(reboots), "bad")
            for nid, why in sorted(reboots.items()):
                self.emit("      node %s x%d  %s\n"
                          % (nid, len(why), ", ".join(why)), "bad")
            # SW_RESTART on an idle fleet is the heap guard firing; PANIC and
            # TASK_WDT are crashes; BROWNOUT is the power rail, not the code.
            # Each points somewhere different, which is the whole reason the
            # reason is now carried on the heartbeat.
            self.emit("    Nothing was racing, so this is its own defect and worth\n"
                      "    chasing independently of drift. SW_RESTART = the heap\n"
                      "    guard; PANIC/TASK_WDT = a crash; BROWNOUT = power.\n", "dim")

        if not fits:
            self.emit("  - No clean series to fit. Need >= 8 samples spanning\n"
                      "    >= 5 min with no restart in the middle.\n", "warn")
            return
        if excluded:
            self.emit("  - Verdict below covers only the %d clean node(s); %s\n"
                      "    contributed nothing.\n"
                      % (len(fits), ", ".join("node %s" % x for x in excluded)), "dim")

        # ── Separate the COMMON MODE from the per-unit signal ────────────────
        #
        # Every ppm here is measured against the MASTER's crystal, so the
        # master's own rate is present, identically, in all of them.  A run
        # where all six nodes read -2.5..-6.1 ppm is not six drifting clients;
        # it is one fast master seen six times.  Reported raw, that common term
        # exceeds the error bars and gets announced as "RESOLVED: nodes 3, 6, 7
        # have real crystal drift" -- attributing the master's offset to three
        # arbitrary clients.
        #
        # It also points the MATERIALITY question at the wrong quantity.  A rate
        # every client shares shifts every lap identically and cancels out of
        # cross-pilot comparison; what can actually mis-order a race is the
        # SPREAD between clients.  So judge on residuals about the fleet median
        # (median, not mean: one genuinely bad crystal must not drag the
        # reference it is being judged against).
        common = None
        if len(fits) >= 3:
            common = statistics.median([p for p, _ in fits.values()])
            resid = {nid: p - common for nid, (p, _) in fits.items()}
            self.emit("\n  - COMMON MODE: every node reads %+.2f ppm against the\n"
                      "    master. That is the MASTER's crystal, not theirs --\n"
                      "    one fast master is a far likelier explanation than %d\n"
                      "    independent crystals all off by the same amount.\n"
                      "    Removing it leaves each node's own rate:\n"
                      % (common, len(fits)), "head")
            for nid in sorted(resid):
                se = fits[nid][1]
                sig = (abs(resid[nid]) / se) if (se == se and se > 0) else 0.0
                self.emit("        node %-2s  %+6.2f ppm  (%.2f sigma)\n"
                          % (nid, resid[nid], sig), "dim")
        else:
            resid = {nid: p for nid, (p, _) in fits.items()}
            self.emit("\n  - Only %d node(s): too few to separate the master's own\n"
                      "    rate from theirs, so the figures below still contain it.\n"
                      % len(fits), "warn")

        # Resolution and materiality are both judged on the RESIDUAL now.
        worst = max(abs(v) for v in resid.values())
        spread = max(resid.values()) - min(resid.values()) if len(resid) > 1 else 0.0
        resolved = [nid for nid, v in resid.items()
                    if fits[nid][1] == fits[nid][1] and fits[nid][1] > 0
                    and abs(v) > 2 * fits[nid][1]]

        self.emit("\n", "dim")
        if resolved:
            self.emit("  - RESOLVED: node(s) %s differ from the fleet by more than\n"
                      "    twice their own error bar, so that IS a per-unit crystal\n"
                      "    rate rather than noise.\n"
                      % ", ".join(str(x) for x in resolved), "ok")
        else:
            self.emit("  - NOT RESOLVED: once the master's common rate is removed,\n"
                      "    every node sits inside its own error bar. The fleet's\n"
                      "    crystals are indistinguishable from each other.\n", "warn")

        # Inter-pilot spread is the number that can actually mis-order a race.
        if worst >= MATERIAL_PPM:
            self.emit("  - MATERIAL: worst node is %.1f ppm from the fleet, moving\n"
                      "    its laps %.1f ms against its rivals across a 5-minute\n"
                      "    race -- above the offset error, so correcting is worth it.\n"
                      "    => gate driftValid on residual, then set CLOCK_APPLY_DRIFT.\n"
                      % (worst, worst * 0.3), "ok")
        else:
            self.emit("  - NOT MATERIAL: the whole fleet spans %.1f ppm = %.1f ms of\n"
                      "    inter-pilot skew across a 5-minute race, below the\n"
                      "    clock-offset error already in the system. Correcting it\n"
                      "    would add noise, not accuracy.\n"
                      "    => leave CLOCK_APPLY_DRIFT off; keep driftPpm as a\n"
                      "       hardware canary only.\n"
                      % (spread, spread * 0.3), "warn")
        if common is not None:
            self.emit("    (master vs clients carries the full %+.1f ppm = %.1f ms,\n"
                      "     and only within one race -- the anchor is re-taken at\n"
                      "     every start, so nothing accumulates across a session.)\n"
                      % (common, abs(common) * 0.3), "dim")

        self.emit("\n  This run was at ONE temperature. A null result here does not\n"
                  "  license disabling drift correction for good -- crystals are\n"
                  "  cut for ~25 C and a unit baking in the sun is the case that\n"
                  "  motivated the feature. Repeat with one node warmed and compare\n"
                  "  its ppm against its neighbours before deciding for the season.\n",
                  "dim")

    def run_fanout(self):
        # DUT only — the probe POSTs over WiFi and reads the master's serial;
        # the emulator is untouched, so its monitor stays live.
        self._start(self._fanout_worker, needs=("DUT",))

    def _fanout_worker(self):
        """Measure the directorState fanout the master cannot measure itself.

        The master only reports the AGGREGATE ("[CORE0] multinode blocked for
        N ms").  That number cannot distinguish "six clients each took 300 ms"
        from "five were instant and one ate the timeout", and those two call
        for completely different fixes.  So we fetch the real payload and time
        a POST of it to each client directly, from the PC, with a timeout long
        enough to measure the truth rather than truncate it at the 300 ms the
        firmware allows.

        Read-only: each client receives the same directorState it already gets
        twice a second, so this cannot disturb a race.
        """
        dut = None
        try:
            ports = self._links()
            if not ports:
                return
            _emu_p, dut_p = ports
            master = self.master_ip.get().strip()

            self.emit("\n" + "=" * 66 + "\n", "dim")
            self.emit("FANOUT PROBE\n", "head")
            self.emit("Times the directorState POST to each client individually.\n"
                      "The firmware allows each one %d ms (connect + read) and fans\n"
                      "out SEQUENTIALLY, so the whole cycle must finish inside\n"
                      "%d ms or parallelTask never gets idle time and SSE starves.\n\n"
                      % (DIRECTOR_FANOUT_MS, DIRECTOR_INTERVAL_MS), "dim")

            # 1. The real payload, exactly as the master fans it out.
            raw, parsed = fetch_director_state(master)
            if raw is None:
                self.emit("  Master at %s did not answer /api/multinode/nodes -- "
                          "is it powered and on this network?\n" % master, "bad")
                return
            self.emit("  Payload: %s bytes\n" % format(len(raw), ","), "head")

            if isinstance(parsed, dict):
                nodes = parsed.get("nodes", []) or []
                laps = 0
                arrays = False
                blockers = []      # online clients not advertising lapSync
                unknown = False    # firmware too old to publish the field
                for n in nodes:
                    if not isinstance(n, dict):
                        continue
                    try:
                        laps = max(laps, int(n.get("lapCount") or 0))
                    except (TypeError, ValueError):
                        pass
                    if isinstance(n.get("laps"), list):
                        arrays = True
                    nid = n.get("nodeId")
                    if not nid:
                        continue          # 0 == the master's own row
                    if "lapSync" not in n:
                        unknown = True
                    elif (n.get("online") and n.get("lapSyncHeard")
                          and not n.get("lapSync")):
                        # Only a node we have HEARD from that did not advertise
                        # lapSync is a blocker; not-yet-heard is not legacy.
                        age = n.get("lastSeenMs")
                        blockers.append((nid, n.get("pilotName") or "?", age))
                self.emit("  Highest lapCount seen: %d\n" % laps, "dim")

                if arrays:
                    self.emit("  Capability gate is SHUT -- nodes still carry full 'laps'\n"
                              "  arrays, so the payload grows with lap count and the heap\n"
                              "  win has not landed.\n", "bad")
                    if blockers:
                        # The gate is all-or-nothing, so ONE node closes it for
                        # the whole fleet. Naming it is the entire point.
                        self.emit("  Held shut by:\n", "bad")
                        for nid, name, age in blockers:
                            extra = ""
                            if isinstance(age, int):
                                extra = "  (last heartbeat %.1f s ago)" % (age / 1000.0)
                                if age > 10000:
                                    extra += "  <-- STALE, heartbeats not arriving"
                            self.emit("    node %-2s %s%s\n" % (nid, name, extra), "bad")
                        self.emit("  A node that is online but never advertises lapSync:1 is\n"
                                  "  either on older firmware or its heartbeats are being\n"
                                  "  rejected (a MAC mismatch 404s the heartbeat, and the\n"
                                  "  capability is only set on the heartbeat path).\n", "dim")
                    elif unknown:
                        self.emit("  Master firmware predates the per-node lapSync field, so\n"
                                  "  the blocker cannot be identified. Re-flash the MASTER to\n"
                                  "  get that diagnostic, then re-run.\n", "warn")
                    else:
                        self.emit("  ODD: every online client advertises lapSync, yet arrays\n"
                                  "  are still being emitted. Check for an node that is\n"
                                  "  registered-but-offline flapping online between the\n"
                                  "  payload build and this fetch.\n", "warn")
                else:
                    self.emit("  Digest-only payload (no per-node lap arrays) -- the\n"
                              "  capability gate is OPEN and payload size is bounded.\n",
                              "good")

            targets = client_targets(parsed)
            if not targets:
                self.emit("  No online clients in the payload -- nothing to probe.\n",
                          "warn")
                return

            # 2. Time each client on its own.
            rounds = 5
            self.emit("\n  Timing %d client(s), %d POSTs each (payload replayed "
                      "verbatim)\n\n" % (len(targets), rounds), "dim")
            results = []
            for nid, ip, _name in targets:
                if self.cancel.is_set():
                    return
                # Reachability first, with a SHORT timeout.  Five 4 s
                # timeouts per node meant an unreachable fleet took two
                # minutes to say so -- long enough to look like a hang.
                probe_ms, probe_status = time_director_post(ip, raw, timeout=1.5)
                if probe_status is None:
                    self.emit("    node %-2s %-15s UNREACHABLE (no response in 1.5 s)\n"
                              % (nid, ip), "bad")
                    results.append((nid, None))
                    continue
                times = [probe_ms]
                fails = 0
                for _ in range(rounds - 1):
                    if self.cancel.is_set():
                        return
                    ms, status = time_director_post(ip, raw, timeout=4.0)
                    if status is None:
                        fails += 1
                    else:
                        times.append(ms)
                    time.sleep(0.15)
                if times:
                    times.sort()
                    med = times[len(times) // 2]
                    over = med > DIRECTOR_FANOUT_MS
                    self.emit("    node %-2s %-15s min=%6.0f  med=%6.0f  max=%6.0f ms%s%s\n"
                              % (nid, ip, times[0], med, times[-1],
                                 "   TIMEOUT-BOUND" if over else "",
                                 ("  (%d failed)" % fails) if fails else ""),
                              "bad" if over else "good")
                    results.append((nid, med))
                else:
                    self.emit("    node %-2s %-15s answered once then stopped "
                              "(%d/%d failed)\n" % (nid, ip, fails, rounds), "bad")
                    results.append((nid, None))

            # 3. What the master itself reported over the same window.
            import re as _re
            dut = JsonLink(dut_p, name="dut", keep_log=True,
                           on_line=self._mon_sink("DUT"))
            self.emit("\n  Sampling the master's own fanout cost for 25 s...\n", "dim")
            blocked = []
            t0 = time.time()
            while time.time() - t0 < 25.0 and not self.cancel.is_set():
                for _ in dut.poll():
                    pass
                for line in dut.log[-40:]:
                    m = _re.search(r"multinode blocked for (\d+) ms", line)
                    if m:
                        v = int(m.group(1))
                        if not blocked or blocked[-1] != v:
                            blocked.append(v)
                time.sleep(0.2)

            # 4. Verdict.
            self.emit("\n  What this means\n", "head")
            timed = [r for r in results if r[1] is not None]
            slow = [r for r in timed if r[1] > DIRECTOR_FANOUT_MS]

            if timed:
                total = sum(r[1] for r in timed)
                self.emit("  - Sum of per-client medians: %.0f ms across %d client(s).\n"
                          % (total, len(timed)), "dim")

            if blocked:
                blocked.sort()
                med_blocked = blocked[len(blocked) // 2]
                self.emit("  - Master reported blocked %d-%d ms (median %d, %d samples).\n"
                          % (blocked[0], blocked[-1], med_blocked, len(blocked)), "dim")
                duty = 100.0 * med_blocked / DIRECTOR_INTERVAL_MS
                tag = "bad" if duty >= 80 else ("warn" if duty >= 50 else "good")
                self.emit("  - Fanout duty cycle: %.0f%% of the %d ms broadcast interval.\n"
                          % (duty, DIRECTOR_INTERVAL_MS), tag)
                if duty >= 80:
                    self.emit("    At this duty parallelTask is effectively always inside\n"
                              "    the fanout, which is what starves SSE and produces\n"
                              "    'not receiving updates' in the browser.\n", "bad")
            else:
                self.emit("  - No '[CORE0] multinode blocked' lines seen. Either the fanout\n"
                          "    is cheap right now, or DEBUG output is being dropped --\n"
                          "    check the Log Panel.\n", "warn")

            if slow:
                names = ", ".join(str(r[0]) for r in slow)
                self.emit("  - SLOW CLIENTS: node(s) %s exceed the %d ms the firmware\n"
                          "    allows, so the master eats its timeout on them every\n"
                          "    broadcast. Fixing those clients (or raising the timeout)\n"
                          "    is worth more than restructuring the fanout.\n"
                          % (names, DIRECTOR_FANOUT_MS), "bad")
            elif timed:
                self.emit("  - Every client answers inside %d ms individually. If the\n"
                          "    master still blocks ~2 s, the cost is the SEQUENTIAL fanout\n"
                          "    itself, not any one slow client -- the fix is to parallelise\n"
                          "    it or lengthen the interval.\n" % DIRECTOR_FANOUT_MS, "warn")
        except Exception as e:
            self.emit("  Fanout probe failed: %s\n" % e, "bad")
        finally:
            if dut:
                try:
                    dut.close()
                except Exception:
                    pass
            self.q.put(("done", None))

    def run_soak(self):
        # DUT only — the soak drives load over WiFi and never opens the
        # emulator, so the EMU monitor keeps logging throughout.
        self._start(self._soak_worker, needs=("DUT",))

    def _soak_worker(self):
        """Hold the device under load and watch heap over TIME, not passes.

        The other tests are bounded by pass count, so they end long before a
        slow allocation problem shows itself — a 90 s run finished with heap
        still above the floor and looked survivable, while a 180 s run at the
        same settings crossed it and the firmware rebooted itself.  What
        matters is the TREND: heap that plateaus is churn being reclaimed,
        heap that declines monotonically will eventually hit the floor no
        matter how healthy any single run looks.

        No emulator or detection involved.  This measures the master under
        multi-node traffic only.
        """
        dut = None
        load = None
        try:
            ports = self._links()
            if not ports:
                return
            emu_p, dut_p = ports
            try:
                mins = float(self.soak_mins.get())
            except ValueError:
                mins = 5.0
            secs = max(30.0, mins * 60.0)

            self.emit("\n" + "=" * 66 + "\n", "dim")
            self.emit("HEAP SOAK\n", "head")
            self.emit(f"Holds the master under multi-node load for {mins:g} "
                      f"minute(s) and tracks heap.\n"
                      f"The firmware reboots ITSELF below 20000 free or 8000 "
                      f"maxBlk sustained 10 s,\nso the question is whether "
                      f"either trends toward those floors.\n\n", "dim")

            dut = JsonLink(dut_p, name="dut", keep_log=True,
                           on_line=self._mon_sink("DUT"))

            load = self._make_load()
            if load:
                load.start()
                self.emit(f"  Load ACTIVE — {self._load_desc()}\n"
                          f"  to node(s) {self.load_nodes.get()} on "
                          f"{self.master_ip.get()}\n\n", "warn")
            else:
                self.emit("  No load configured — this measures IDLE heap "
                          "behaviour only.\n\n", "warn")

            import re as _re
            samples = []          # (t_s, free, maxBlk)
            t0 = time.time()
            last_report = 0.0
            rebooted = False
            while time.time() - t0 < secs and not self.cancel.is_set():
                for _ in dut.poll():
                    pass                       # JSON not needed; drives on_line
                for line in dut.log[-40:]:
                    m = _re.search(r"\[HEAP\] free=(\d+) min=(\d+) maxBlk=(\d+)", line)
                    if not m:
                        continue
                    rec = (int(m.group(1)), int(m.group(2)), int(m.group(3)))
                    if not samples or samples[-1][1:] != (rec[0], rec[2]):
                        samples.append((time.time() - t0, rec[0], rec[2]))
                if any("Initializing storage" in l for l in dut.log[-40:]):
                    rebooted = True
                    break
                el = time.time() - t0
                if el - last_report >= 30.0:
                    last_report = el
                    if samples:
                        _, f, b = samples[-1]
                        self.emit(f"    t+{el:4.0f}s   free={f:<7} maxBlk={b:<7}"
                                  f"  ({len(samples)} samples)\n", "dim")
                time.sleep(0.2)

            if load and load.started:
                load.stop()
                self.emit(f"\n  Load stopped: {load.sent} POST(s) accepted, "
                          f"{load.failed} failed\n", "dim")

            self.emit("\n  What this means\n", "head")
            if rebooted:
                self.emit("  - THE DEVICE REBOOTED during the soak. That is the "
                          "answer: it cannot sustain this load.\n", "bad")
                self._check_for_reboot(dut)
                return
            if len(samples) < 3:
                self.emit("  - Too few [HEAP] samples to judge. They are logged "
                          "every 5 s; run longer.\n", "warn")
                return

            # Judge the SECOND HALF only.  Heap settles sharply in the first
            # minute as caches fill and clients register, and an
            # endpoint-to-endpoint slope is dominated by that settling — it
            # reported "DECLINING, 1 minute to the floor" for a run whose maxBlk
            # had been dead flat at 14324 for the previous two minutes.  What
            # matters is whether it is STILL falling once steady state is
            # reached, not how far it fell getting there.
            half = samples[len(samples) // 2:]
            if len(half) < 3:
                half = samples
            t_span = (half[-1][0] - half[0][0]) or 1e-9
            d_free = half[-1][1] - half[0][1]
            d_blk  = half[-1][2] - half[0][2]
            min_free = min(x[1] for x in samples)
            min_blk  = min(x[2] for x in samples)
            free_rate = (d_free / t_span) * 60.0
            blk_rate  = (d_blk  / t_span) * 60.0

            self.emit(f"  - SETTLING (first half): free {samples[0][1]} -> "
                      f"{half[0][1]}, maxBlk {samples[0][2]} -> {half[0][2]}. "
                      f"Expected as caches fill.\n", "dim")
            self.emit(f"  - STEADY STATE (last {t_span:.0f}s): free {half[0][1]} "
                      f"-> {half[-1][1]} ({d_free:+}), maxBlk {half[0][2]} -> "
                      f"{half[-1][2]} ({d_blk:+}).\n"
                      f"    Lowest seen overall: free {min_free}, "
                      f"maxBlk {min_blk}.\n", "dim")
            self.emit(f"  - RATE (steady state): free {free_rate:+.0f} "
                      f"bytes/min, maxBlk {blk_rate:+.0f} bytes/min.\n", "dim")

            # maxBlk is what actually trips the watchdog, so project on it too.
            worst = None
            if free_rate < -200:
                worst = ("free", (half[-1][1] - 20000) / (-free_rate))
            if blk_rate < -200:
                t_blk = (half[-1][2] - 8000) / (-blk_rate)
                if worst is None or t_blk < worst[1]:
                    worst = ("maxBlk", t_blk)

            # A flat second half is the success condition and deserves saying
            # plainly, rather than being left to infer from a small slope.
            if abs(d_blk) < 1500 and abs(d_free) < 8000:
                worst = None
                self.emit(f"  - PLATEAU: maxBlk held at ~{half[-1][2]} and free "
                          f"at ~{half[-1][1]} across the last {t_span:.0f}s.\n"
                          f"    Allocation churn is being reclaimed — this is "
                          f"what a fixed heap looks like.\n", "good")

            if worst and worst[1] > 0:
                self.emit(f"  - DECLINING: at this rate {worst[0]} reaches its "
                          f"floor in about {worst[1]:.0f} more minute(s), and "
                          f"the firmware\n    will reboot itself. This is a "
                          f"real problem, not test noise.\n", "bad")
            elif worst:
                self.emit(f"  - ALREADY BELOW the {worst[0]} floor — a reboot is "
                          f"imminent.\n", "bad")
            else:
                self.emit(f"  - STABLE: neither figure is trending down "
                          f"meaningfully. Allocation churn is being reclaimed, "
                          f"so\n    heap is not the limiting factor at this "
                          f"load.\n", "good")
                if min_blk < 12000:
                    self.emit(f"    Note: maxBlk dipped to {min_blk}, within "
                              f"1.5x of the 8000 floor. Stable but not roomy.\n",
                              "warn")
        except Exception as e:
            self.emit(f"\nERROR: {e}\n", "bad")
        finally:
            try:
                if load and load.started:
                    load.stop()
            except Exception:
                pass
            if dut:
                dut.close()
            self.q.put(("done", None))

    def _build_buttons(self, root):
        # Wrapping row: seven test buttons plus the run controls are wider than
        # the window's own minimum, so on anything but a wide desktop the later
        # tests used to sit off-screen with no scrollbar to reach them.
        # Outer spacing via pack rather than ttk padding: place() coordinates
        # are relative to the widget's own origin and do not account for a ttk
        # frame's internal padding, so padding here would clip the bottom row
        # by however much was set.
        f = FlowFrame(root)
        f.pack(fill="x", padx=10, pady=4)
        self.btn_row = f

        self.btn_level = f.add(ttk.Button(f, text="1. Check Analog Path",
                                          command=self.run_level))
        self.btn_thresh = f.add(ttk.Button(f, text="2. Set Thresholds",
                                           command=self.run_thresholds))
        self.btn_interval = f.add(ttk.Button(f, text="3. Accuracy + Consistency",
                                             command=self.run_interval))
        self.btn_sweep = f.add(ttk.Button(f, text="4. Min Pass Width (Sweep)",
                                          command=self.run_sweep))
        self.btn_soak = f.add(ttk.Button(f, text="5. Heap Soak",
                                         command=self.run_soak))
        self.btn_fanout = f.add(ttk.Button(f, text="6. Fanout Probe",
                                           command=self.run_fanout))
        self.btn_drift = f.add(ttk.Button(f, text="7. Clock Drift Log",
                                          command=self.run_drift))
        self.btn_sync = f.add(ttk.Button(f, text="8. Race Sync",
                                         command=self.run_race_sync))

        f.add(ttk.Label(f, text="sync rounds:"), gap_before=10)
        self.sync_rounds = tk.StringVar(value="3")
        f.add(ttk.Entry(f, textvariable=self.sync_rounds, width=4))

        # gap_before marks a group boundary, so when the row wraps it prefers
        # to break between groups rather than mid-control.
        f.add(ttk.Label(f, text="soak mins:"), gap_before=10)
        self.soak_mins = tk.StringVar(value="5")
        f.add(ttk.Entry(f, textvariable=self.soak_mins, width=5))

        # Drift needs its OWN duration.  It used to share the soak's box, which
        # defaults to 5 -- and a 5-minute drift run yields ~2 samples per node,
        # below the 8-sample floor, so the tool simply refused to answer.  The
        # two runs want opposite defaults: a soak is short, a drift fit is long.
        f.add(ttk.Label(f, text="drift mins:"), gap_before=10)
        self.drift_mins = tk.StringVar(value="60")
        f.add(ttk.Entry(f, textvariable=self.drift_mins, width=5))

        self.btn_stop = f.add(ttk.Button(f, text="Stop", command=self.stop_run,
                                         state="disabled"), gap_before=10)
        f.add(ttk.Button(f, text="Clear", command=self.clear))

    def _build_output(self, root):
        f = ttk.LabelFrame(root, text="Results", padding=6)
        f.pack(fill="both", expand=True, padx=10, pady=(4, 10))

        # height is a FLOOR, not a target.  This is the only widget packed with
        # expand=True, so it absorbs whatever the window has left after the
        # fixed rows above it — which is how the pane grows to ~48 rows on the
        # desktop and shrinks gracefully on a laptop.  Requesting 48 here
        # instead would make the window's own requested size exceed a small
        # screen, and Tk would then clip the button row rather than the pane.
        self.out = scrolledtext.ScrolledText(f, wrap="word", height=12,
                                             font=("Consolas", 9))
        self.out.pack(fill="both", expand=True)
        style_text_widget(self.out)
        # Status colours are lifted toward the light end: the saturated red and
        # green that read well on white go muddy and low-contrast on a dark
        # ground, which is exactly where a "bad" line must not be easy to miss.
        self.out.tag_config("head", font=("Consolas", 10, "bold"),
                            foreground=HEAD_FG)
        self.out.tag_config("good", foreground=OK_FG)
        self.out.tag_config("ok",   foreground=OK_FG)
        self.out.tag_config("warn", foreground=WARN_FG)
        self.out.tag_config("bad",  foreground=BAD_FG)
        self.out.tag_config("dim",  foreground=MUTED)

        self.status = ttk.Label(root, text="Ready", style="Status.TLabel",
                                anchor="w")
        self.status.pack(fill="x", side="bottom")

    # -- helpers ------------------------------------------------------------

    # Where the chosen ports are remembered between sessions.  Keyed by USB
    # serial number, not COM port: COM numbers move when devices are re-plugged,
    # while the serial number is stable.
    _PREFS_PATH = os.path.join(os.path.dirname(os.path.abspath(__file__)),
                               "rig_settings.json")

    def _load_prefs(self):
        try:
            with open(self._PREFS_PATH, "r", encoding="utf-8") as fh:
                return json.load(fh)
        except Exception:
            return {}

    def _write_prefs(self, prefs):
        try:
            with open(self._PREFS_PATH, "w", encoding="utf-8") as fh:
                json.dump(prefs, fh, indent=2, sort_keys=True)
            return True
        except Exception as e:
            self.log(f"Could not save settings: {e}\n", "warn")
            return False

    def _load_port_prefs(self):
        return self._load_prefs().get("ports", {})

    def _save_port_prefs(self, ports):
        prefs = self._load_prefs()
        prefs["ports"] = ports
        self._write_prefs(prefs)

    def _setting_vars(self):
        """Every tk variable that represents a user setting.

        Discovered by type rather than listed by hand, so a setting added later
        is saved automatically instead of being silently forgotten — the usual
        way these files rot.
        """
        found = {}
        for name, val in vars(self).items():
            if name.startswith("_"):
                continue
            if isinstance(val, (tk.StringVar, tk.BooleanVar,
                                tk.IntVar, tk.DoubleVar)):
                found[name] = val
        for key, val in getattr(self, "vars", {}).items():
            found[f"vars.{key}"] = val        # the Signal spinboxes
        return found

    def save_settings(self):
        prefs = self._load_prefs()
        prefs["settings"] = {k: v.get() for k, v in self._setting_vars().items()}
        if self._write_prefs(prefs):
            self.log(f"Saved {len(prefs['settings'])} setting(s). They will be "
                     f"restored next time the GUI starts.\n", "good")

    def reset_settings(self):
        """Back to the values the GUI ships with, and forget the saved ones.

        Without this, one bad saved value (a 60000 ms interval, load pointed at
        a stale IP) persists across every future launch with no obvious way out
        short of deleting the file by hand.
        """
        for name, var in self._setting_vars().items():
            if name in getattr(self, "_defaults", {}):
                try:
                    var.set(self._defaults[name])
                except Exception:
                    pass
        prefs = self._load_prefs()
        prefs.pop("settings", None)          # ports are kept deliberately
        self._write_prefs(prefs)
        self.log("Settings reset to defaults and the saved copy cleared. "
                 "Remembered ports are kept.\n", "good")

    def restore_settings(self, quiet=False):
        saved = self._load_prefs().get("settings", {})
        if not saved:
            return
        applied = 0
        for name, var in self._setting_vars().items():
            if name not in saved:
                continue
            try:
                var.set(saved[name])
                applied += 1
            except Exception:
                pass      # a stale or renamed setting must not stop the rest
        if applied and not quiet:
            self.log(f"Restored {applied} saved setting(s).\n", "dim")

    @staticmethod
    def _serial_of(label):
        """Pull the USB serial number back out of a combobox label."""
        parts = label.split("  ")
        return parts[2].strip() if len(parts) >= 3 else ""

    def remember_ports(self):
        """Pin the current selections by USB serial number.

        Stored as serial numbers rather than COM ports because COM numbers are
        reassigned on re-plug, while the serial number (the device MAC on ESP32
        native USB) identifies one specific unit forever.
        """
        prefs = self._load_port_prefs()
        dut_sn = self._serial_of(self.dut_cb.get())
        emu_sn = self._serial_of(self.emu_cb.get())
        if dut_sn and dut_sn != "no-serial":
            prefs["dut"] = dut_sn
        if emu_sn and emu_sn != "no-serial":
            prefs["emu"] = emu_sn
        self._save_port_prefs(prefs)
        self.log(f"Remembered: FPVRaceOne={prefs.get('dut','-')}  "
                 f"emulator={prefs.get('emu','-')}\n"
                 f"  These are matched by serial number from now on, whatever "
                 f"COM port they land on.\n", "good")

    def refresh_ports(self):
        ports = list(list_ports.comports())
        prefs = self._load_port_prefs()
        labels, emu_guess, dut_guess = [], None, None
        pref_emu_label, pref_dut_label = None, None
        for p in ports:
            vid = f"{p.vid:04X}" if p.vid else "????"
            # On ESP32 native USB the serial number IS the device MAC, which is
            # the only reliable way to tell the master from its client units —
            # they all enumerate as 303A:1001 with identical descriptions.
            sn = p.serial_number or "no-serial"
            label = f"{p.device}  [{vid}]  {sn}  {p.description[:28]}"
            labels.append(label)
            if sn and sn == prefs.get("dut"):
                pref_dut_label = label
            if sn and sn == prefs.get("emu"):
                pref_emu_label = label
            # Same discriminator the upload task uses: Espressif native USB
            # (0x303A) is the XIAO C6; a bridge chip is the WROOM-32 devkit.
            if p.vid == 0x303A and dut_guess is None:
                dut_guess = label
            elif p.vid in (0x10C4, 0x1A86, 0x0403) and emu_guess is None:
                emu_guess = label

        self.emu_cb["values"] = labels
        self.dut_cb["values"] = labels

        # Auto-pick by USB VID, but never override a choice already made and
        # still present.  Every client unit is also a 0x303A ESP32-C6, so
        # "first native-USB port found" is not reliably the master — once the
        # operator has picked the right one, a refresh must not silently move
        # the test to a different device.
        # Priority: remembered serial number > current selection > VID guess.
        def _pick(cb, remembered, guess):
            if remembered:
                cb.set(remembered)
                return remembered, True
            cur = cb.get()
            if cur and cur in labels:
                return cur, False        # still connected — leave it alone
            if guess:
                cb.set(guess)
                return guess, False
            return None, False

        _pick(self.emu_cb, pref_emu_label, emu_guess)
        dut_sel, dut_remembered = _pick(self.dut_cb, pref_dut_label, dut_guess)

        self.log(f"Found {len(ports)} serial port(s).\n", "dim")
        if dut_remembered:
            self.log(f"  FPVRaceOne restored from saved serial "
                     f"{self._serial_of(dut_sel)} on {dut_sel.split()[0]}.\n", "good")
        else:
            n303a = sum(1 for p in ports if p.vid == 0x303A)
            if n303a > 1 and dut_sel:
                self.log(f"  {n303a} devices share VID 0x303A (client units are "
                         f"ESP32-C6 too). Pick the master, then press Remember "
                         f"Ports\n  so it is matched by serial number "
                         f"(= its MAC) from now on.\n", "warn")

    @staticmethod
    def _port_of(label):
        return label.split()[0] if label else None

    # ── Live serial monitor ────────────────────────────────────────────
    def _autostart_monitor(self):
        """Deferred launch start — re-check the toggle at FIRE time.

        Checking only at schedule time was a race: switching the monitor off
        within the first 300 ms still let it grab the ports afterwards, so the
        checkbox and reality disagreed.
        """
        if self.monitor_on.get():
            self._start_monitor()

    def _toggle_monitor(self):
        if self.monitor_on.get():
            self._start_monitor()
        else:
            self._stop_monitor()

    def _start_monitor(self, watch=("DUT", "EMU"), quiet=False):
        """Start the raw-serial monitor over `watch` ports only.

        `watch` exists so a test that claims one port does not silence the
        other.  The soak and the fanout probe only ever open the DUT, so the
        emulator has no reason to go dark for five minutes — and a gap in the
        EMU log during a run is exactly when you want to know whether the
        emulator was still alive.
        """
        if self._mon_thread and self._mon_thread.is_alive():
            return
        if not watch:
            return
        if self.worker and self.worker.is_alive() and set(watch) & self._mon_claimed:
            self.log("Cannot monitor a port a running test has claimed.\n", "warn")
            return
        ports = self._links()
        if not ports:
            self.monitor_on.set(False)
            return
        emu_p, dut_p = ports
        self._mon_stop.clear()
        self._mon_thread = threading.Thread(
            target=self._monitor_worker, args=(emu_p, dut_p, tuple(watch)),
            daemon=True)
        self._mon_thread.start()
        if quiet:
            # _stop_monitor() unticked the box on its way out.  Re-tick it:
            # the monitor IS running, just on fewer ports, and a checkbox
            # reading "off" while the EMU pane fills up is worse than useless.
            # Same programmatic .set() the done-handler already relies on, so
            # it does not re-enter the widget command.
            self.monitor_on.set(True)
            names = ", ".join(sorted(watch))
            self.log(f"  Live monitor continues on {names} "
                     f"(the other port is held by the test).\n", "dim")
            return
        self.log(f"Live monitor ON — FPVRaceOne {dut_p}, emulator {emu_p}. "
                 f"Raw output, nothing filtered.\n"
                 f"  Open 'Log Panel' to view it. The ports are held while "
                 f"monitoring, so untick Live monitor before flashing from "
                 f"PlatformIO.\n", "good")

    def _stop_monitor(self):
        self._mon_stop.set()
        t = self._mon_thread
        if t:
            t.join(timeout=2.0)
        self._mon_thread = None
        self.monitor_on.set(False)

    def _monitor_worker(self, emu_p, dut_p, watch=("DUT", "EMU")):
        """Read the watched ports raw and stream them to the log panel.

        Deliberately does NOT parse or filter.  Every diagnostic gap this
        session came from a filter dropping the one line that mattered — the
        panic, the [HEAP] FATAL, the [CORE0] stall.  Raw means raw.

        Each port reconnects independently.  Both boards reset in normal use —
        the master on its own low-heap watchdog, the emulator when its port is
        opened — and a monitor that gave up on the first read error would go
        silent precisely when something interesting had just happened.
        """
        all_targets = {"DUT": dut_p, "EMU": emu_p}
        targets = {k: v for k, v in all_targets.items() if k in watch}
        handles = {}          # name -> serial handle (absent = needs opening)
        buffers = {k: "" for k in targets}
        next_try = {k: 0.0 for k in targets}
        announced = set()

        def _open(name):
            now = time.time()
            if now < next_try[name]:
                return
            next_try[name] = now + 2.0        # retry cadence while unplugged
            try:
                handles[name] = open_port_no_reset(targets[name])
                if name in announced:
                    self.emit_mon_status(name, f"  Monitor: {name} reconnected "
                                               f"on {targets[name]}.\n", "good")
                    announced.discard(name)
            except Exception as e:
                if name not in announced:
                    hint = ""
                    if "denied" in str(e).lower() or "access" in str(e).lower():
                        hint = ("\n     Another program holds that port — a "
                                "PlatformIO/VSCode serial monitor, PuTTY, or a "
                                "second copy\n     of this GUI. Close it and "
                                "the monitor will reconnect on its own.")
                    self.emit_mon_status(name,
                        f"  Monitor: cannot open {name} on {targets[name]} — "
                        f"{e}{hint}\n", "bad")
                    announced.add(name)

        try:
            while not self._mon_stop.is_set():
                for name in targets:
                    if name not in handles:
                        _open(name)
                        continue
                    try:
                        data = handles[name].read(4096).decode("utf-8",
                                                               errors="replace")
                    except Exception as e:
                        # Port vanished (board reset / cable). Drop it and let
                        # the reconnect loop pick it up again.
                        try:
                            handles[name].close()
                        except Exception:
                            pass
                        handles.pop(name, None)
                        self.emit_mon_status(name, f"  Monitor: {name} "
                                                   f"disconnected — {e}\n", "bad")
                        announced.add(name)
                        continue
                    if not data:
                        continue
                    buffers[name] += data
                    while "\n" in buffers[name]:
                        line, buffers[name] = buffers[name].split("\n", 1)
                        line = line.rstrip("\r")
                        if not line:
                            continue
                        stamp = time.strftime("%H:%M:%S")
                        rec = f"{stamp} [{name}] {line}"
                        lines = self._mon_lines[name]
                        lines.append(rec)
                        if len(lines) > self._MON_MAX_LINES:
                            del lines[:len(lines) - self._MON_MAX_LINES]
                        tag = self._mon_tag(line)
                        # The emulator heartbeat carries tickHz — the timer ISR
                        # rate.  It should sit at TICK_HZ whether or not a run
                        # is playing, so zero means the DAC has stopped being
                        # driven.  Call that out rather than leave an operator
                        # to notice one number among thousands of lines.
                        if name == "EMU" and '"event":"hb"' in line.replace(" ", ""):
                            m = re.search(r'"tickHz"\s*:\s*(\d+)', line)
                            if m:
                                hz = int(m.group(1))
                                if hz == 0:
                                    tag = "bad"
                                    self.emit_mon(name,
                                        "--- EMULATOR DAC STOPPED: tickHz=0, the "
                                        "envelope timer ISR is not running ---\n",
                                        "bad")
                                elif hz < 9000 or hz > 11000:
                                    tag = "warn"
                        if name == "EMU" and '"rst"' in line and "POWERON" not in line \
                                and "EXT_RESET" not in line:
                            self.emit_mon(name,
                                "--- EMULATOR RESTARTED for a non-normal reason "
                                "(see rst= above) ---\n", "bad")
                        self.emit_mon(name, rec + "\n", tag)
                time.sleep(0.02)
        finally:
            for sp in handles.values():
                try:
                    sp.close()
                except Exception:
                    pass
            self.emit("  Live monitor OFF.\n", "dim")

    def save_logs(self):
        """Write the monitor buffers and the on-screen results to text files."""
        out_dir = os.path.join(os.path.dirname(os.path.abspath(__file__)), "logs")
        try:
            os.makedirs(out_dir, exist_ok=True)
        except Exception as e:
            self.log(f"Could not create {out_dir}: {e}\n", "bad")
            return
        stamp = time.strftime("%Y%m%d-%H%M%S")
        written = []
        for name in ("DUT", "EMU"):
            lines = self._mon_lines.get(name, [])
            if not lines:
                continue
            path = os.path.join(out_dir, f"{stamp}-{name.lower()}-serial.txt")
            try:
                with open(path, "w", encoding="utf-8") as fh:
                    fh.write("\n".join(lines) + "\n")
                written.append((path, len(lines)))
            except Exception as e:
                self.log(f"Could not write {path}: {e}\n", "bad")
        # The results pane too — that is what actually gets shared.
        try:
            path = os.path.join(out_dir, f"{stamp}-results.txt")
            with open(path, "w", encoding="utf-8") as fh:
                fh.write(self.out.get("1.0", "end"))
            written.append((path, None))
        except Exception as e:
            self.log(f"Could not write results: {e}\n", "bad")

        if not written:
            self.log("Nothing to save yet — turn the live monitor on, or run a "
                     "test first.\n", "warn")
            return
        self.log(f"Saved {len(written)} file(s) to {out_dir}\n", "good")
        for path, n in written:
            self.log(f"   {os.path.basename(path)}"
                     f"{f'  ({n} lines)' if n else ''}\n", "dim")

    def log(self, text, tag=None):
        self.out.insert("end", text, tag or "")
        self.out.see("end")

    def clear(self):
        self.out.delete("1.0", "end")

    def _busy(self, busy):
        state = "disabled" if busy else "normal"
        for b in (self.btn_level, self.btn_thresh, self.btn_interval,
                  self.btn_sweep, self.btn_soak, self.btn_fanout,
                  self.btn_drift, self.btn_sync):
            b.config(state=state)
        self.btn_stop.config(state="normal" if busy else "disabled")
        self.status.config(text="Running…" if busy else "Ready")

    def _ints(self):
        try:
            return {k: int(v.get()) for k, v in self.vars.items()}
        except ValueError:
            self.log("Settings must be whole numbers.\n", "bad")
            return None

    def _links(self):
        emu_p = self._port_of(self.emu_cb.get())
        dut_p = self._port_of(self.dut_cb.get())
        if not emu_p or not dut_p:
            self.log("Select both serial ports first.\n", "bad")
            return None
        if emu_p == dut_p:
            self.log("Emulator and FPVRaceOne cannot be the same port.\n", "bad")
            return None
        return emu_p, dut_p

    def _open_emu(self, emu_p):
        """Open the emulator port and CONFIRM it booted before using it.

        Opening the port asserts DTR/RTS, which hardware-resets the WROOM-32.
        The fixed settle in JsonLink is a guess; if the board is slow the
        commands that follow land in the bootloader and vanish.  The emulator
        then sits at baseline and every pass reads as missed — indistinguishable
        from a device-side detection failure, which is exactly how a run of 30
        passes reported 0 laps.
        """
        # keep_log=True: the emulator is an ESP32 and prints a panic message,
        # backtrace and ROM boot banner to the same serial port it speaks JSON
        # on.  Without capture those lines were discarded, so a crashing rig was
        # invisible and its runs looked like device detection failures.
        emu = JsonLink(emu_p, name="emu", keep_log=True,
                       on_line=self._mon_sink("EMU"))
        if emulator_handshake(emu) is None:
            emu.close()
            self.emit(
                "  Emulator did not respond to 'ping' after opening the port.\n"
                "  It resets when the port opens; if it is slow to boot the run\n"
                "  would silently generate nothing. Re-run, or check the cable\n"
                "  and port selection.\n", "bad")
            return None
        return emu

    def stop_run(self):
        self.cancel.set()
        self.status.config(text="Stopping…")

    def _start(self, fn, *a, needs=("DUT", "EMU")):
        if self.worker and self.worker.is_alive():
            # Silently ignoring this read as a hang: the button simply did
            # nothing and the results pane stayed empty.
            self.log("A test is already running — stop it first.\n", "warn")
            return
        # Release ONLY the ports this test actually opens.  Stopping the whole
        # monitor left the emulator unlogged for the entire run, so a five
        # minute soak showed a five minute hole in the EMU capture — precisely
        # the window where you want to know the emulator was still alive.
        self._mon_claimed = set(needs)
        keep = tuple(n for n in ("DUT", "EMU") if n not in self._mon_claimed)
        if self._mon_thread and self._mon_thread.is_alive():
            self._mon_resume_after_test = True
            self._stop_monitor()
            if keep:
                self._start_monitor(watch=keep, quiet=True)
            else:
                self.log("Live monitor paused for the test; it will resume "
                         "after.\n", "dim")
        self.cancel.clear()
        self._busy(True)
        self.worker = threading.Thread(target=fn, args=a, daemon=True)
        self.worker.start()

    def _drain(self):
        """Pump worker messages onto the Tk thread."""
        try:
            while True:
                kind, payload = self.q.get_nowait()
                if kind == "log":
                    text, tag = payload
                    self.log(text, tag)
                elif kind == "mon":
                    name, text, tag = payload
                    self._log_write(name, text, tag)
                elif kind == "done":
                    self._busy(False)
                    # Release the claim BEFORE restarting, or _start_monitor
                    # refuses the ports the finished test was holding.
                    self._mon_claimed = set()
                    if self._mon_resume_after_test:
                        self._mon_resume_after_test = False
                        self._stop_monitor()          # drop any partial watch
                        self.monitor_on.set(True)
                        self._start_monitor()
        except queue.Empty:
            pass
        self.root.after(100, self._drain)

    # ── Raw-serial side panel ──────────────────────────────────────────
    @staticmethod
    def _mon_tag(line):
        """Colour for a raw serial line. Shared so the live monitor and the
        during-test sink highlight the same things."""
        if any(k in line for k in ("FATAL", "Guru", "panic", "rst:",
                                   "assert", "Backtrace")):
            return "bad"
        if any(k in line for k in ("timed out", "WARN", "blocked")):
            return "warn"
        return "dim"

    def _mon_sink(self, name):
        """Callback that pushes one device's serial lines into the log panel.

        Given to JsonLink during tests so the panels keep filling while the
        monitor is paused.  Everything lands in the same _mon_lines buffers, so
        Save Logs produces one continuous record of the session rather than
        only the gaps between tests.
        """
        def sink(line):
            stamp = time.strftime("%H:%M:%S")
            rec = f"{stamp} [{name}] {line}"
            buf = self._mon_lines.setdefault(name, [])
            buf.append(rec)
            if len(buf) > self._MON_MAX_LINES:
                del buf[:len(buf) - self._MON_MAX_LINES]
            self.emit_mon(name, rec + "\n", self._mon_tag(line))
        return sink

    def emit_mon_status(self, name, text, tag=None):
        """Monitor connection status — shown in the MAIN pane as well.

        Status was previously sent only to the log panel, so "port unavailable"
        was invisible whenever that window happened to be closed: the operator
        saw an empty pane and no reason for it.  The most important message
        must not live in the window you might not have open.
        """
        self.emit(text, tag)
        self.q.put(("mon", (name, text, tag)))

    def emit_mon(self, name, text, tag=None):
        """Queue a raw serial line for the log panel (thread-safe)."""
        self.q.put(("mon", (name, text, tag)))

    def _autodock_log_panel(self):
        if self.log_panel_auto.get():
            self.open_log_panel(dock=True)

    def _dock_geometry(self, panel_w=760):
        """Geometry string placing the panel flush right of the main window.

        Falls back to the left side when there is not enough room, rather than
        pushing the panel off-screen where it cannot be reached.
        """
        self.root.update_idletasks()
        mx, my = self.root.winfo_x(), self.root.winfo_y()
        mw, mh = self.root.winfo_width(), self.root.winfo_height()
        sw, sh = self.root.winfo_screenwidth(), self.root.winfo_screenheight()

        h = max(400, min(mh, sh - my - 40))
        right_edge = mx + mw
        if right_edge + panel_w <= sw:
            x = right_edge                     # flush right, no gap
        elif mx - panel_w >= 0:
            x = mx - panel_w                   # no room right: dock left
        else:
            panel_w = max(480, sw - right_edge)  # squeeze into what is left
            x = max(0, sw - panel_w)
        return f"{panel_w}x{h}+{x}+{my}"

    def open_log_panel(self, dock=False):
        """Two stacked raw-serial panes in a separate window.

        Separate from the results pane because the monitor runs for hours and
        would otherwise bury the test output — which is the part that gets
        saved and shared.  Stacked rather than side-by-side so long firmware
        lines stay readable without wrapping.
        """
        if self._log_win is not None and tk.Toplevel.winfo_exists(self._log_win):
            if dock:
                self._log_win.geometry(self._dock_geometry())
            self._log_win.lift()
            self._log_win.focus_force()
            return

        win = tk.Toplevel(self.root)
        # A Toplevel gets the system background, not the ttk theme's — without
        # this the log window keeps a light frame around dark panes.
        win.configure(bg=BG)
        win.title("Raw serial — FPVRaceOne / emulator")
        # Undocked was a hardcoded 980x760, which overhangs a 1366x768 laptop.
        # _dock_geometry() already clamps itself; this is the other path.
        win.geometry(self._dock_geometry() if dock
                     else fit_to_screen(win, 980, 760, min_w=640, min_h=400))
        # Docked, but not always-on-top: it must be possible to put another
        # window over it without the panel fighting back.
        win.transient(self.root)
        self._log_win = win
        self._log_text = {}
        self._log_follow = {}

        for name, title in (("DUT", "FPVRaceOne (device under test)"),
                            ("EMU", "RX5808 emulator")):
            frame = ttk.LabelFrame(win, text=title, padding=4)
            frame.pack(fill="both", expand=True, padx=6, pady=(6, 3))

            bar = ttk.Frame(frame)
            bar.pack(fill="x")
            follow = tk.BooleanVar(value=True)
            self._log_follow[name] = follow
            ttk.Checkbutton(bar, text="Follow", variable=follow).pack(side="left")
            ttk.Button(bar, text="Clear",
                       command=lambda n=name: self._log_clear(n)).pack(side="left", padx=4)
            ttk.Label(bar, text="(raw, unfiltered)", foreground=MUTED,
                      font=("", 8)).pack(side="left", padx=6)

            txt = scrolledtext.ScrolledText(frame, wrap="none", height=18,
                                            font=("Consolas", 9))
            txt.pack(fill="both", expand=True)
            style_text_widget(txt)
            txt.tag_config("bad", foreground=BAD_FG)
            txt.tag_config("warn", foreground=WARN_FG)
            txt.tag_config("dim", foreground=MUTED)
            self._log_text[name] = txt

        # Backfill whatever the monitor already captured, so opening the panel
        # mid-session shows history instead of starting blank.
        for name in ("DUT", "EMU"):
            for line in self._mon_lines.get(name, [])[-2000:]:
                self._log_write(name, line + "\n", None, backfill=True)

        win.protocol("WM_DELETE_WINDOW", self._close_log_panel)

    def _close_log_panel(self):
        # Closing it is an explicit choice; remember it so the next launch
        # honours the same decision.
        self.log_panel_auto.set(False)
        # Buffers survive in _mon_lines, so closing loses nothing and Save Logs
        # still works.
        if self._log_win is not None:
            try:
                self._log_win.destroy()
            except Exception:
                pass
        self._log_win = None
        self._log_text = {}
        self._log_follow = {}

    def _log_clear(self, name):
        txt = self._log_text.get(name)
        if txt:
            txt.delete("1.0", "end")

    def _log_write(self, name, text, tag, backfill=False):
        txt = self._log_text.get(name)
        if txt is None:
            return                    # panel closed; _mon_lines still has it
        txt.insert("end", text, tag or "")
        # Bound the widget independently of the memory buffer — Tk slows badly
        # once a text widget holds tens of thousands of lines.
        if not backfill and int(txt.index("end-1c").split(".")[0]) > 5000:
            txt.delete("1.0", "1000.0")
        follow = self._log_follow.get(name)
        if follow is None or follow.get():
            txt.see("end")

    def emit(self, text, tag=None):
        self.q.put(("log", (text, tag)))

    def check_master(self):
        """Confirm the master is reachable and report which nodes are
        registered — POSTing to an unregistered nodeId is rejected with 404,
        which would produce a load run that silently does nothing."""
        ip = self.master_ip.get().strip()
        self.log(f"\nProbing master at {ip} ...\n", "dim")
        data = probe_master(ip)
        if not data:
            self.log(f"  No response. Is this PC associated with the master's "
                     f"AP, and is {ip} correct?\n", "bad")
            return
        nodes = data.get("nodes", []) if isinstance(data, dict) else []
        clients = [n for n in nodes if not n.get("isMaster")]
        online = [n for n in clients if n.get("online")]
        self.log(f"  Master reachable. {len(clients)} client(s) registered, "
                 f"{len(online)} online.\n", "good" if online else "warn")
        for n in clients:
            self.log(f"    node {n.get('nodeId')}  "
                     f"{'online ' if n.get('online') else 'OFFLINE'}  "
                     f"{n.get('pilotName','')}\n", "dim")
        if online:
            ids = ",".join(str(n.get("nodeId")) for n in online)
            self.load_nodes.set(ids)
            self.log(f"  Node IDs set to: {ids}\n", "dim")
        else:
            self.log("  No online clients — load POSTs would be rejected (404) "
                     "and the fanout would have no targets.\n", "bad")
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
